bgates747/agon-extender/docs/tasks/README.md

# Project Tasks

This directory contains the tracked detail record for every item in `TODO.md`.
Task files hold scope, instructions, state, decisions, evidence, gotchas, and
validation requirements; `TODO.md` remains the authoritative task index.

Keep private network and filesystem topology, credentials, account data, and
unique device identifiers out of tracked tasks. Refer to an ignored local
record when such details are operationally necessary.

## Task silos and durable promotion

Use task directories as bounded work and review silos while scope, evidence,
and implementation shape are still emerging. Keeping each task's generators,
schemas, evidence, and provisional outputs together makes its contribution
discrete and auditable without prematurely declaring project-wide structure.

When a task-local result becomes recurring infrastructure or documentation,
promote it into a durable role-named location rather than leaving production
users dependent on a historical task number. Promotion preserves the task
record and accepted evidence, but the maintained interface, procedures, tools,
and canonical artifacts move under the subject they serve.

A durable construct may synthesize accepted work from several task silos. The
promotion task must identify the contributing authorities, remove competing
machine-readable sources of truth, update routine references, and preserve
traceability without copying task history into the production interface.

## Current documentation versus evidence

The [current handbook](../README.md) is the operating/design entry point for
humans and agents. When accepted work changes behavior, update its maintained
role-named guide in place so that it contains only currently accurate guidance.
Do not require readers to reconcile an old instruction with a later amendment.

Task records, dated experiments and historical decisions preserve provenance;
they are not competing current manuals. Move reusable guidance to its maintained
authority and link that authority from the task. Keep superseded instructions
in Git history or clearly separated evidence, not beneath a warning in the
current procedure. Unknown implementation/qualification limits remain explicit
current facts; do not erase those limits to make the handbook look finished.

## Actor-explicit proposals

The `TRS-80-NNN` namespace owns Extender integration work for TRS-80-derived
software and systems. `TRS-80-001` begins with TRS-OS on Agon; the namespace
does not imply that physical TRS-80 hardware or every TRS-80 model is supported.
`TODO.md` remains the sole authoritative unfinished-task index.

Every proposed contract, decision, task, procedure, and failure path must name
the actor performing each material action. Identify the applicable eZ80/MOS
component, onboard VDP/Pico-D4 firmware, EDP/P4 firmware, hardware circuit,
physical wiring, host tool, resident service, application, or operator rather
than assigning behavior vaguely to “the system” or “firmware.”

For communication, name the sender, receiver, transport owner, and physical
wiring where known. Distinguish the actor requesting an action from the actor
authorizing, executing, recording, observing, and recovering it. If ownership
is genuinely unresolved, say so explicitly and assign the decision to a
tracked task.

## Firmware defect identities

Use the stable `FWBUG-NNN` identity from [the firmware bug register](../firmware-bugs.md)
for a promoted defect task (`docs/tasks/FWBUG-NNN.md`), rather than renumbering
it. Register findings before implementation; link the originating task records
back to the register item and retain their historical finding IDs. Promotion
requires a corresponding TODO entry and bounded work contract; a bug register
entry alone does not start work.

## Tested acceptance closes into production

Explicit Author approval after testing authorizes the owning agent to promote
that accepted result into the maintained production location as part of closeout.
Package exact tested bytes, verify and retain the new immutable bundle, update
`production/current.yaml` and the current handbook/operating guides, then commit
and tag the promotion with the agreed production version. Keep rollback and
bounded evidence. Do not leave accepted deliverables only in a task silo.

The version must already be approved, or the agent must obtain that decision.
An annotated immutable Git tag identifies the commit containing the selected
bundle and documentation; push the commit and tag under the Author's repository
publication authorization. Existing tags and archived bundles are not rewritten.
See [versioning policy](../versions/README.md). This does not start unrelated
work or authorize public distribution of private/local-only archives.
