bgates747/agon-extender/docs/tasks/SETUP-006/SETUP-006.4-wiring-design/electrical-requirements.md

# SETUP-006.4 electrical requirements and candidate allocation

> **Historical task evidence:** HW-001 superseded this provisional allocation
> with the common-UART `light2-harness-r02` candidate. This file remains useful
> for predecessor evidence and requirement provenance but is not current wiring
> authority.

## Status and interpretation

- State: task-local review candidate
- Physical assembly: unchanged
- Author's completed Fritzing source draft: wiring and geometry preserved;
  embedded UART1 labels corrected by CA-2026-08-25-001
- Fritzing `draft_v1` derivative: generated for Author review
- Immediate target: Exclusive Extended beta transport
- Separate deferred target: Exclusive Compatible stock UART

This review turned the then-current firmware and mode requirements into
electrical design inputs. It does not approve a harness revision, claim that
the assembled bench matches the candidate, or authorize a physical test.

The generated `draft_v1` has separately been corrected and machine-audited as
a complete drawing of the controlled-power predecessor circuit under
AUDIT-002. It is evidence and a construction reference for that circuit, not a
claim that the fresh-design allocation below has already been drawn or
accepted.

The predecessor `light2-harness-r01` pin map and its runs are strong
evidence for the enhanced forward bus. They are not proof of assembled-system
safety and are not a stock-VDP UART design. The latter requires a later design
review after EMOS and EDP freeze its physical requirements.

## Pinned sources

1. Official VDP tag `v2.16.0`, commit
   `c7ac293d2aa81ddfa693390549bcd909069c8fc3`: `video/agon.h`,
   `video/vdp_protocol.h`, `video/vdu_sys.h`, and
   `video/vdu_stream_processor.h`.
2. Official MOS commit `5f67b1ca77eb7a77d3b37cc7b029db51f0d1548e`:
   `main.c`, `src/uart.c`, and `src/serial.asm`.
3. Olimex ESP32-P4-DevKit commit
   `4b453612bd72e2b83b49cb1156de93f655b8aec4`, Rev D1 schematic
   `HARDWARE/ESP32-P4-DevKit-Rev.D1/ESP32-P4-DevKit_Rev_D1.kicad_sch`.
4. Current project authorities: PORT-008, QUAL-002, the operating-mode audit,
   and `hardware/designs/light2-harness-r01/`.
5. TI's current SN74LV125A documentation identifies over-voltage-tolerant
   inputs and `Ioff` partial-power-down support. TI's SN74HC125 documentation
   identifies input clamp diodes and does not specify `Ioff`. At least four
   exact TI `SN74LV125AN` 14-PDIP parts are operator-confirmed on order. Receipt,
   physical count, and allocation to Extender remain unconfirmed because the
   separately ordered parts may be committed elsewhere.

## Contract layers

The phrase "compatible transport" must not collapse three different contracts:

1. **Application bytes:** EDP consumes the same VDU command bytes and emits the
   same VDP protocol packets as official VDP for retained functionality.
2. **EMOS behavior:** EMOS owns routing, response parsing, completion flags,
   sysvar updates, activation, committed mode, and recovery.
3. **Physical transport:** Exclusive Extended uses an eight-bit forward bus and
   a one-way UART return. It need not copy the onboard VDP's four-wire UART0
   circuit, but it must prove equivalent application-visible behavior, pacing,
   and recovery within the accepted mode contract.

Official VDP uses 1,152,000-baud 8-N-1 UART, begins with RTS flow control, and
can enable CTS/RTS full duplex. Official MOS UART0 provides RX, TX, RTS, and CTS
on Port D bits 0 through 3. Current official MOS UART1 provides PC0 TX and PC1
RX, while its hardware-flow helper configures PC3 only as CTS input; it does
not currently provide a UART1 RTS output on PC2. Exclusive Extended therefore
cannot assume that stock UART0 electrical flow control exists on UART1.

## Immediate beta signal inventory

### Mandatory conductors and local controls
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
