bgates747/agon-extender/docs/tasks/QUAL-003/debrief/P01h/codec-screen/discussion/2026-09-17-gemini-architecture.md

### Architectural Specification: Agon Light/Console 8 ESP32-P4 Extender Board

This document defines the system architecture, dual-core resource allocation, memory maps, and configuration parameters for using the **Olimex ESP32-P4-DevKit-Rev-D1** as a high-performance Video Display Processor (VDP) network extender for the **Agon Light 2** and **Heber Console 8** (eZ80F92/F91). 

### 1. System Architecture & Dual-Core Topology

To sustain a **512x384 1bpp single-buffered framebuffer** transmission over a 100 Mbps RMII Ethernet link without blocking or lagging real-time command processing from the eZ80, the system relies on strict **Symmetric Multiprocessing (SMP)** segregation. 

                  +---------------------------------------+

                  |         eZ80 Host Computer            |
                  +---------------------------------------+
                                      |
                                      | (UART over Port C Pins)
                                      v
+-------------------------------------------------------------------------+

| Olimex ESP32-P4 Extender Board                                          |
|                                                                         |
|  +-----------------------------------+   +----------------------------+ |
|  | Core 1 (APP_CPU): VDP Emulation   |   | Core 0 (PRO_CPU): Network  | |
|  |-----------------------------------|   |----------------------------| |
|  | * Deep Internal SRAM UART FIFO    |   | * LwIP TCP/IP Stack        | |
|  | * Decodes Agon VDP Packets        |   | * Ethernet MAC/PHY Drivers | |
|  | * Modifies Live Framebuffer       |   | * Lockless Frame Snapshot  | |
|  +-----------------------------------+   +----------------------------+ |
|                    |                                    ^               |
|                    v (Direct Write)                     | (Lockless Copy|
|        +-----------------------+                        |  sub-uS speed)|
|        | vdp_framebuffer       |------------------------+               |
|        | (24 KB Aligned SRAM)  |                                        |
|        +-----------------------+                                        |
|                                                                         |
|  +--------------------------------------------------------------------+ |
|  | GDMA & Network Hardware Layer                                      | |
|  |--------------------------------------------------------------------| |
|  | Outbound Stream Buffer (Internal SRAM)                             | |
|  | LAN8720 RMII Ethernet Controller Interface                         | |
|  +--------------------------------------------------------------------+ |
+-------------------------------------------------------------------------+
                                      |
                                      v
                         +--------------------------+

                         | Network Target / Client  |
                         +--------------------------+
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
