bgates747/agon-extender/docs/tasks/BENCH-001/evidence/driving-hour.png

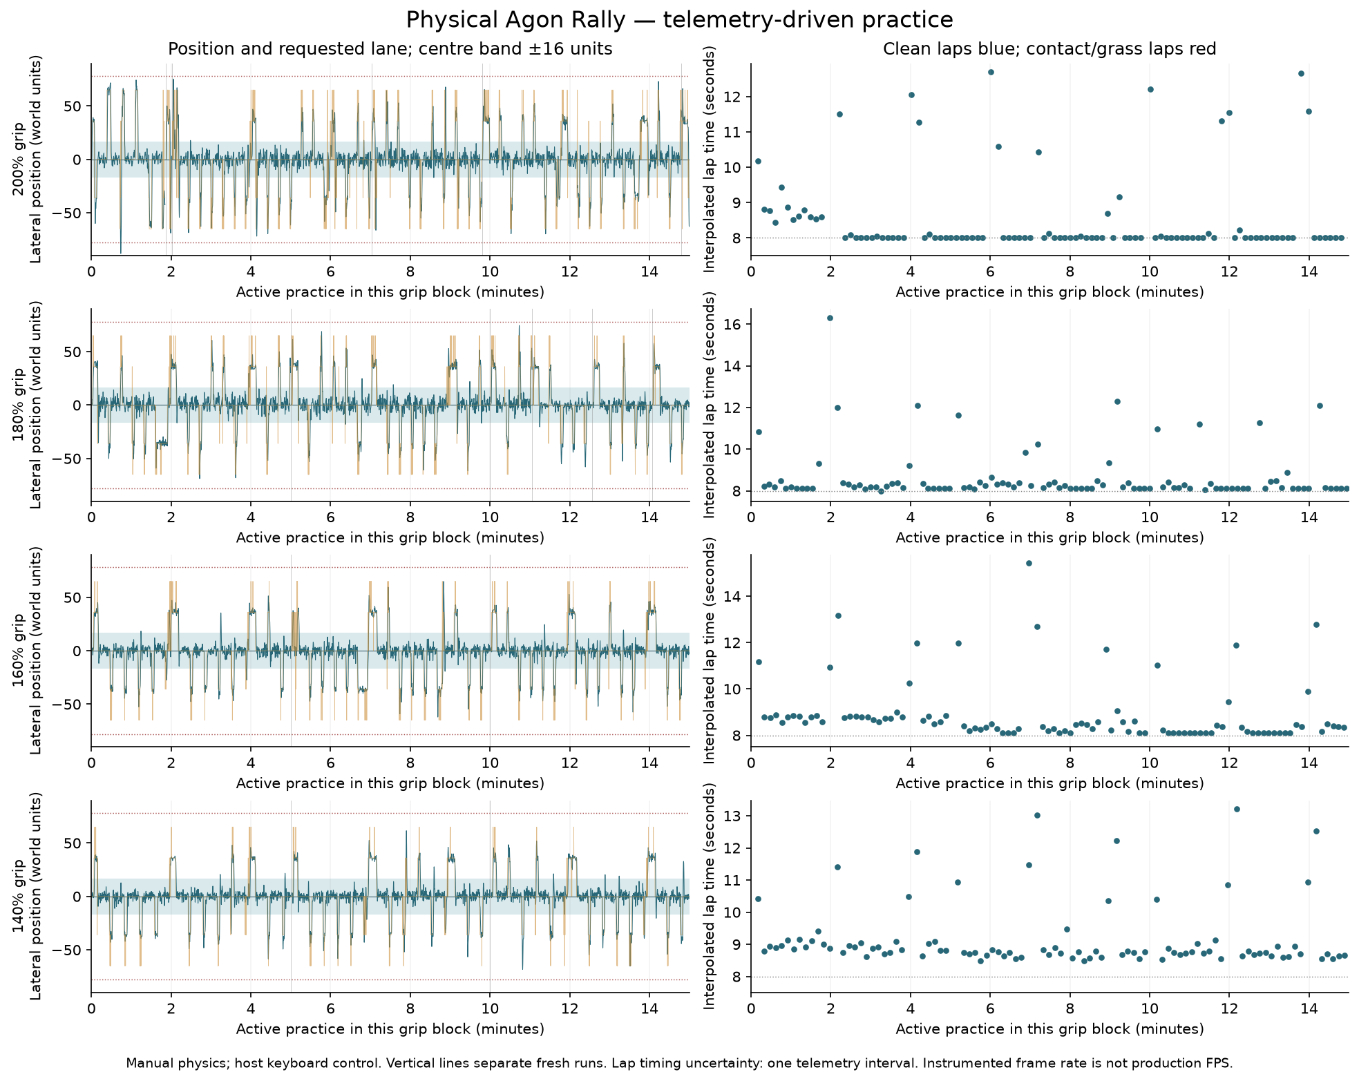
docs/tasks/BENCH-001/evidence/driving-hour.png
