bgates747/agon-extender/docs/tasks/QUAL-003/debrief/P01f/A/rtos-tasks.png

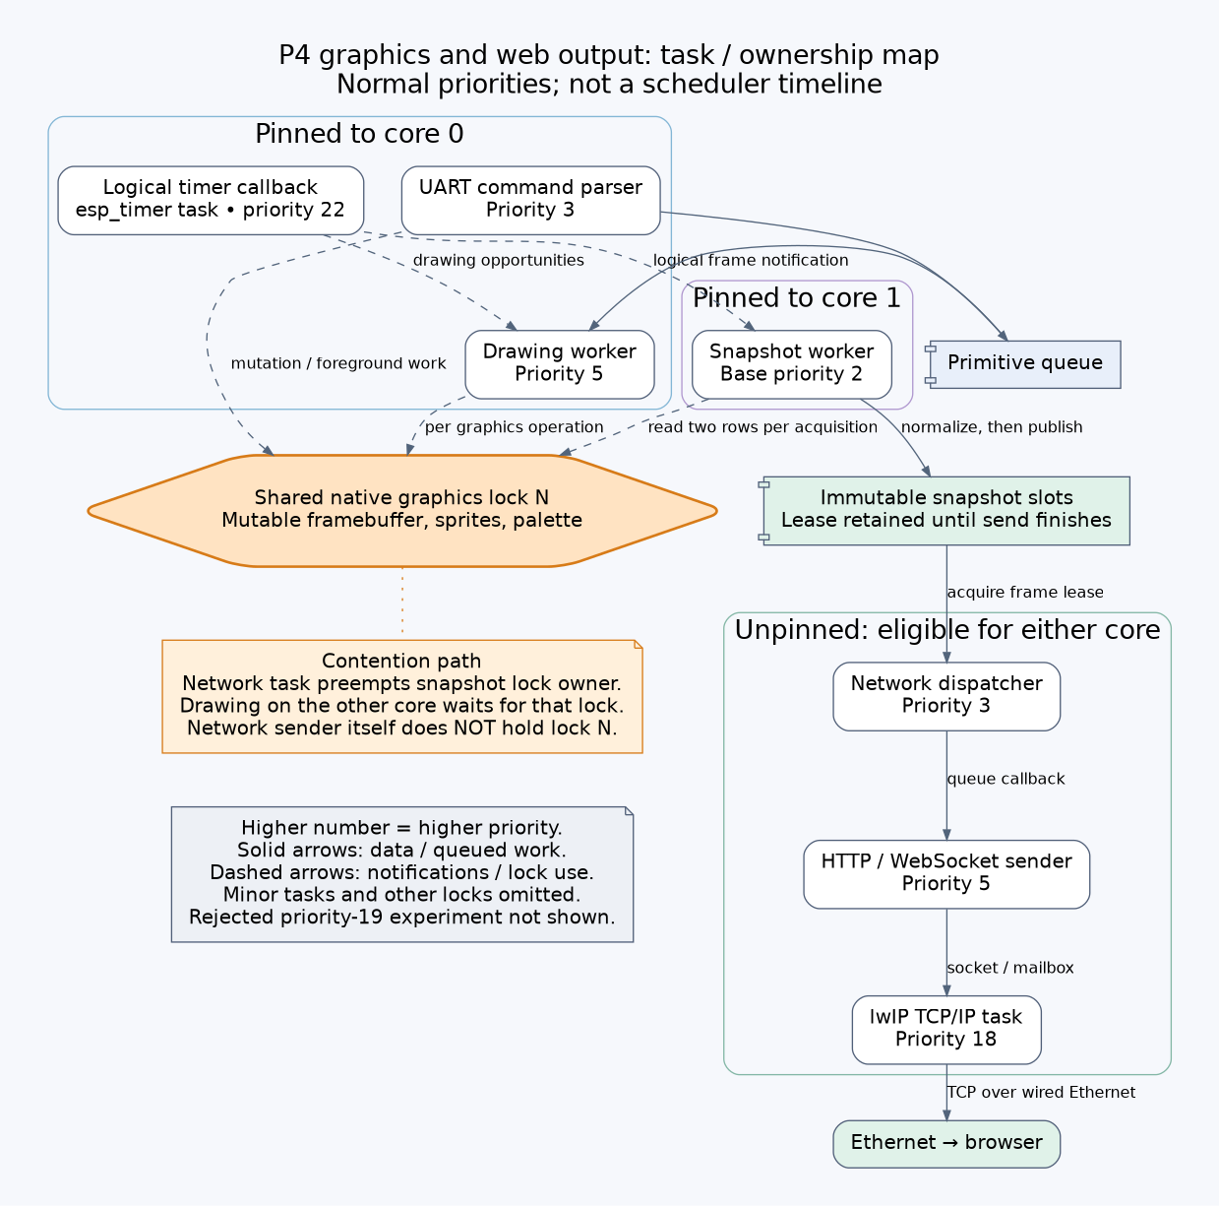
docs/tasks/QUAL-003/debrief/P01f/A/rtos-tasks.png
