bgates747/agon-extender/docs/tasks/QUAL-003/debrief/P01g/ladder.png

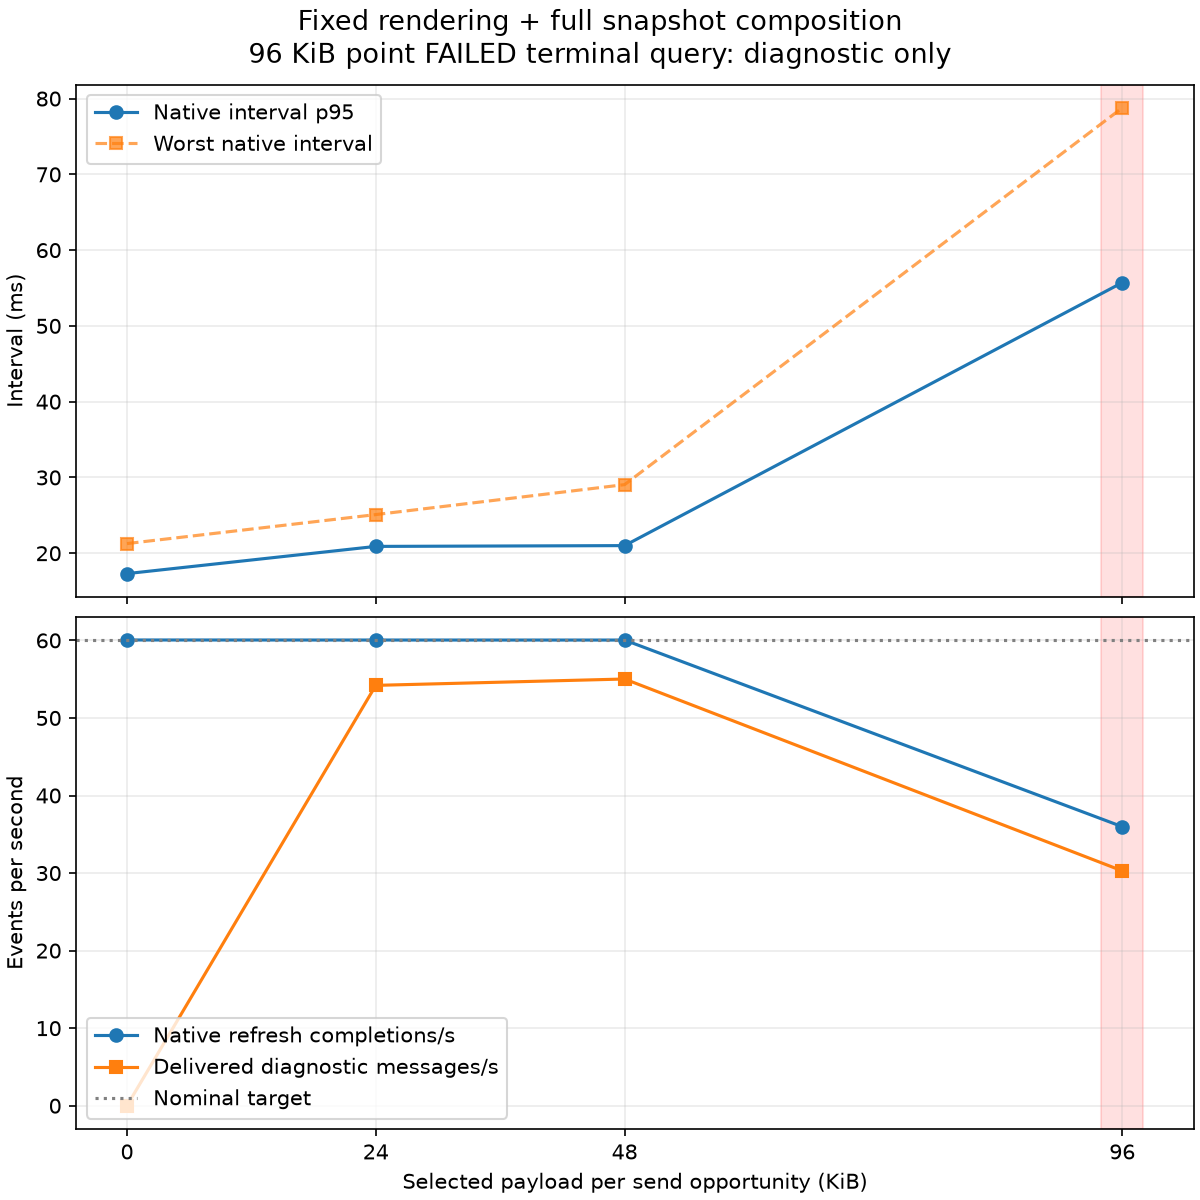
docs/tasks/QUAL-003/debrief/P01g/ladder.png
