bgates747/agon-extender/docs/tasks/QUAL-003/debrief/P01h/codec-screen/image-p4/images/nurples-jpeg90.png

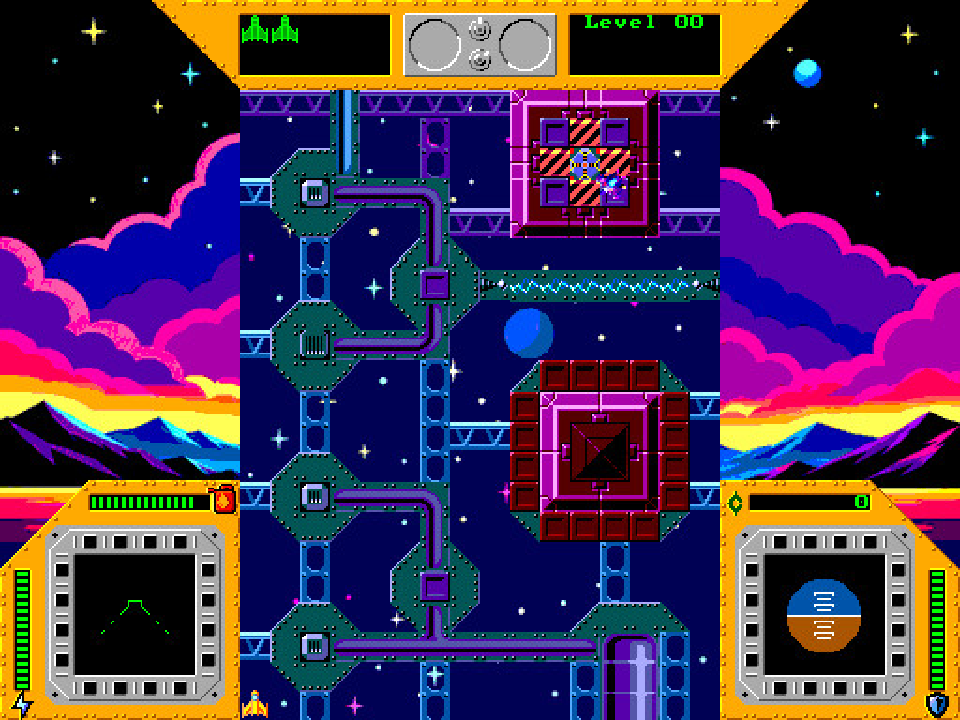
docs/tasks/QUAL-003/debrief/P01h/codec-screen/image-p4/images/nurples-jpeg90.png
