bgates747/agon-extender/docs/tasks/QUAL-003/debrief/P01h/evidence/raw_sprites-r06.png

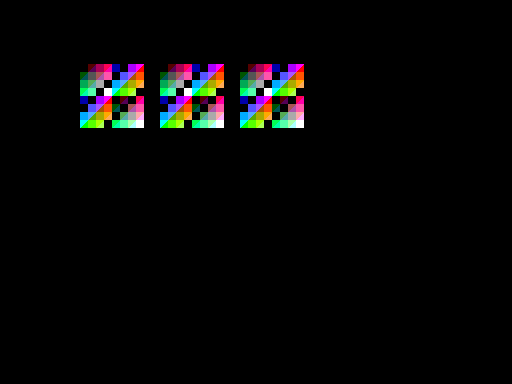
docs/tasks/QUAL-003/debrief/P01h/evidence/raw_sprites-r06.png
