bgates747/agon-extender/docs/tasks/QUAL-003/debrief/P01h/srle2/web/evidence/final/rejected-frame-retains-image.png

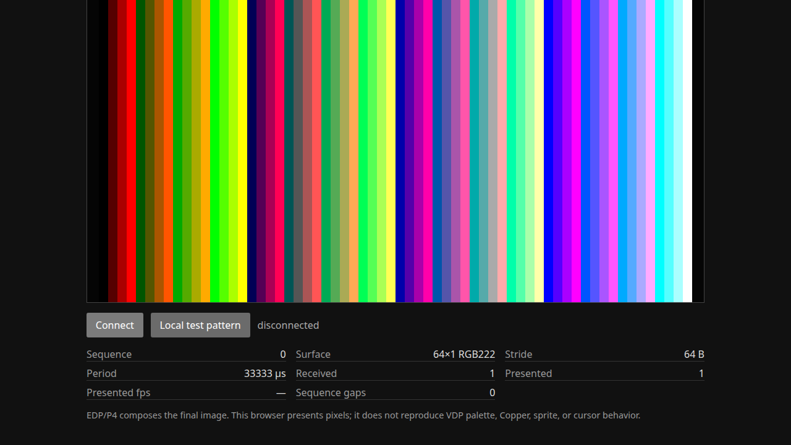
docs/tasks/QUAL-003/debrief/P01h/srle2/web/evidence/final/rejected-frame-retains-image.png
