bgates747/agon-extender/docs/tasks/QUAL-004/evidence/bounded-corpus/BSP26_01-a2/BSP26_01/mainboard.png

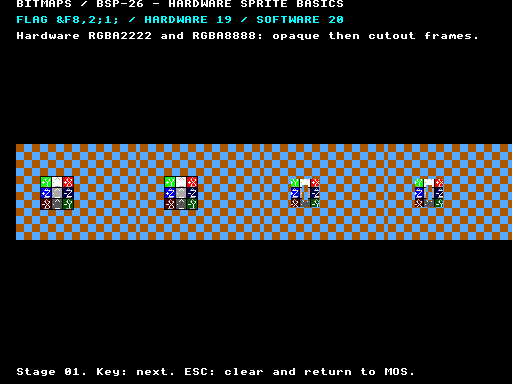
docs/tasks/QUAL-004/evidence/bounded-corpus/BSP26_01-a2/BSP26_01/mainboard.png
