bgates747/agon-extender/docs/tasks/QUAL-004/evidence/bounded-corpus/BSP26_02-a1/BSP26_02/mainboard.png

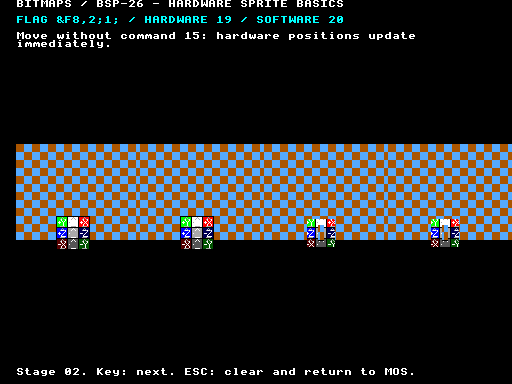
docs/tasks/QUAL-004/evidence/bounded-corpus/BSP26_02-a1/BSP26_02/mainboard.png
