bgates747/agon-extender/docs/tasks/QUAL-004/evidence/bounded-corpus/BSP26_03-a1/BSP26_03/mainboard.png

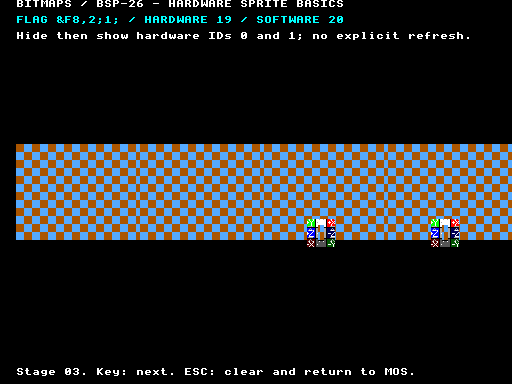
docs/tasks/QUAL-004/evidence/bounded-corpus/BSP26_03-a1/BSP26_03/mainboard.png
