bgates747/agon-extender/docs/tasks/QUAL-004/evidence/bounded-corpus/BSP27_01-a1/BSP27_01/mainboard.png

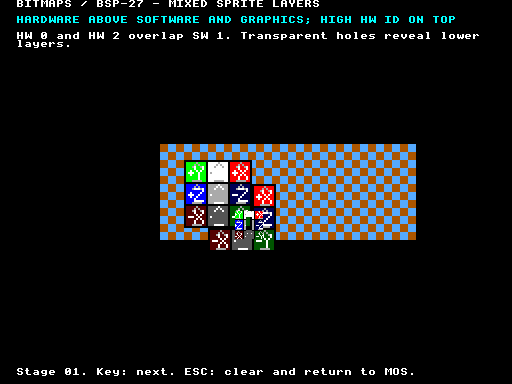
docs/tasks/QUAL-004/evidence/bounded-corpus/BSP27_01-a1/BSP27_01/mainboard.png
