bgates747/agon-extender/docs/tasks/QUAL-004/evidence/bounded-corpus/CLIPROW-a1/CLIPROW/mainboard.png

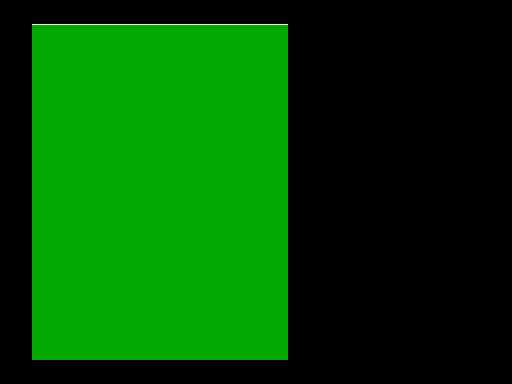
docs/tasks/QUAL-004/evidence/bounded-corpus/CLIPROW-a1/CLIPROW/mainboard.png
