bgates747/agon-extender/docs/tasks/QUAL-004/evidence/bounded-corpus/SHP01-a1/SHP01/mainboard.png

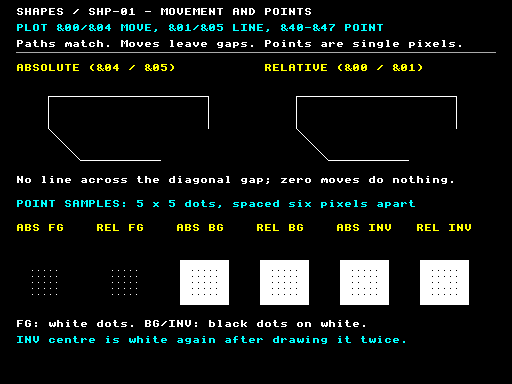
docs/tasks/QUAL-004/evidence/bounded-corpus/SHP01-a1/SHP01/mainboard.png
