bgates747/agon-extender/docs/tasks/QUAL-004/evidence/bounded-corpus/SHP02-a1/SHP02/mainboard.png

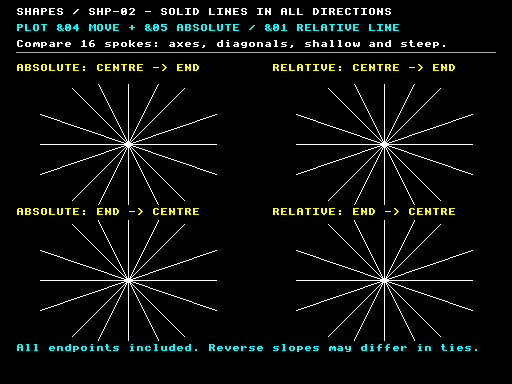
docs/tasks/QUAL-004/evidence/bounded-corpus/SHP02-a1/SHP02/mainboard.png
