bgates747/agon-extender/docs/tasks/QUAL-004/evidence/bounded-corpus/SHP03-a1/SHP03/mainboard.png

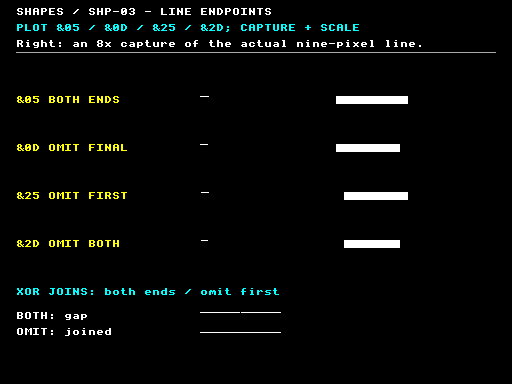
docs/tasks/QUAL-004/evidence/bounded-corpus/SHP03-a1/SHP03/mainboard.png
