bgates747/agon-extender/docs/tasks/QUAL-004/evidence/bounded-corpus/SHP04-a1/SHP04/mainboard.png

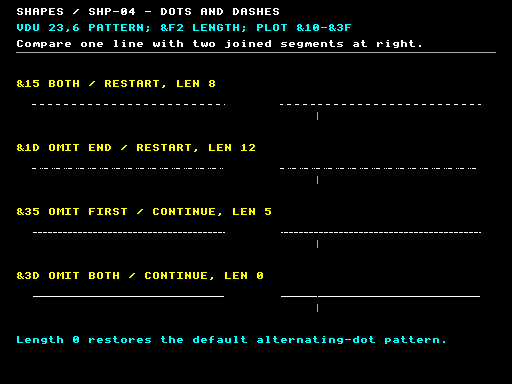
docs/tasks/QUAL-004/evidence/bounded-corpus/SHP04-a1/SHP04/mainboard.png
