bgates747/agon-extender/docs/tasks/QUAL-004/evidence/bounded-corpus/SHP05-a1/SHP05/mainboard.png

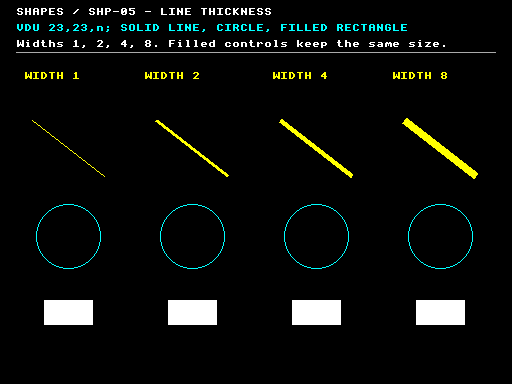
docs/tasks/QUAL-004/evidence/bounded-corpus/SHP05-a1/SHP05/mainboard.png
