bgates747/agon-extender/docs/tasks/QUAL-004/evidence/bounded-corpus/SHP06-a1/SHP06/mainboard.png

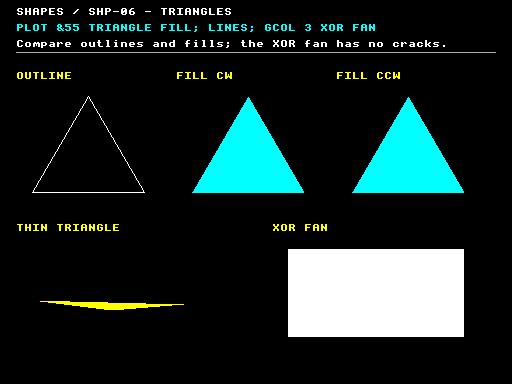
docs/tasks/QUAL-004/evidence/bounded-corpus/SHP06-a1/SHP06/mainboard.png
