bgates747/agon-extender/docs/tasks/QUAL-004/evidence/bounded-corpus/SHP07-a1/SHP07/mainboard.png

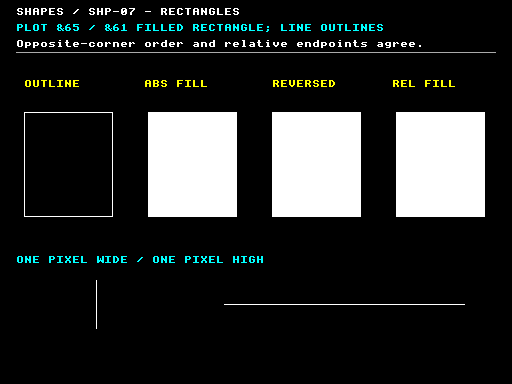
docs/tasks/QUAL-004/evidence/bounded-corpus/SHP07-a1/SHP07/mainboard.png
