bgates747/agon-extender/docs/tasks/QUAL-004/evidence/bounded-corpus/SHP08-a1/SHP08/mainboard.png

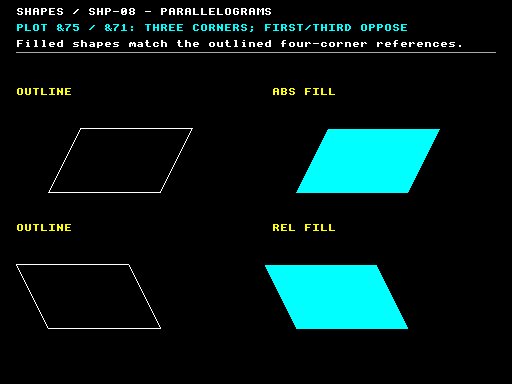
docs/tasks/QUAL-004/evidence/bounded-corpus/SHP08-a1/SHP08/mainboard.png
