bgates747/agon-extender/docs/tasks/QUAL-004/evidence/bounded-corpus/SHP09-a1/SHP09/mainboard.png

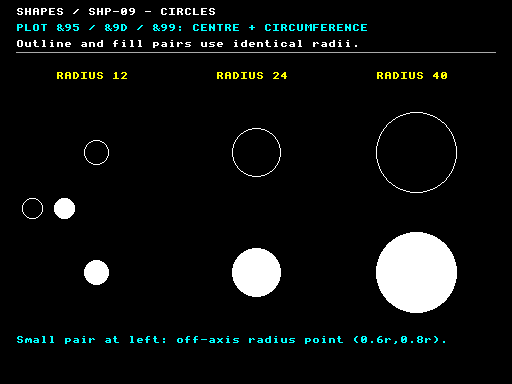
docs/tasks/QUAL-004/evidence/bounded-corpus/SHP09-a1/SHP09/mainboard.png
