bgates747/agon-extender/docs/tasks/QUAL-004/evidence/bounded-corpus/SHP10-a1/SHP10/mainboard.png

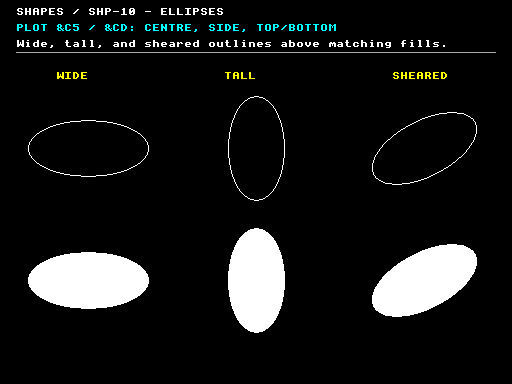
docs/tasks/QUAL-004/evidence/bounded-corpus/SHP10-a1/SHP10/mainboard.png
