bgates747/agon-extender/docs/tasks/QUAL-004/evidence/bounded-corpus/SHP11-a1/SHP11/mainboard.png

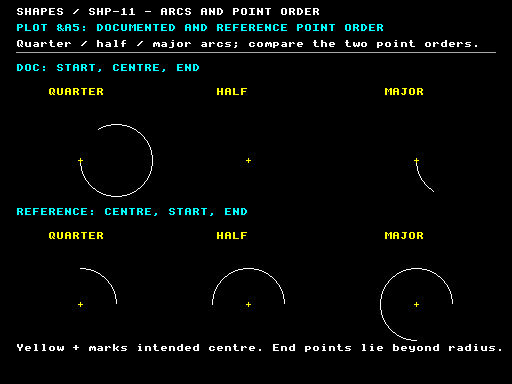
docs/tasks/QUAL-004/evidence/bounded-corpus/SHP11-a1/SHP11/mainboard.png
