bgates747/agon-extender/docs/tasks/QUAL-004/evidence/bounded-corpus/SHP12-a1/SHP12/mainboard.png

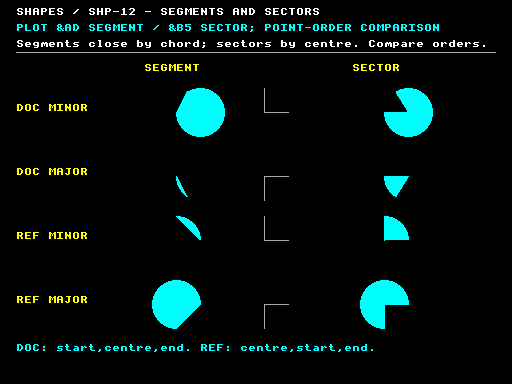
docs/tasks/QUAL-004/evidence/bounded-corpus/SHP12-a1/SHP12/mainboard.png
