bgates747/agon-extender/docs/tasks/QUAL-004/evidence/bounded-corpus/SHP13-a1/SHP13/mainboard.png

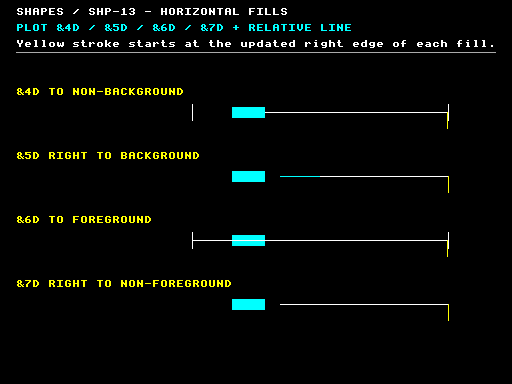
docs/tasks/QUAL-004/evidence/bounded-corpus/SHP13-a1/SHP13/mainboard.png
