bgates747/agon-extender/docs/tasks/QUAL-004/evidence/bounded-corpus/SHP14-a1/SHP14/mainboard.png

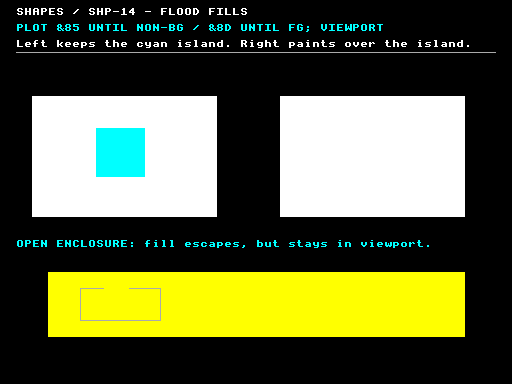
docs/tasks/QUAL-004/evidence/bounded-corpus/SHP14-a1/SHP14/mainboard.png
