bgates747/agon-extender/docs/tasks/QUAL-004/evidence/bounded-corpus/SHP15-a1/SHP15/mainboard.png

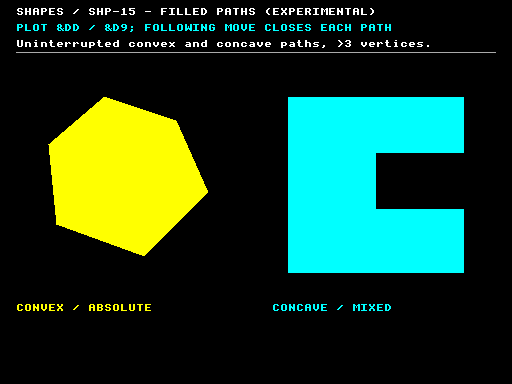
docs/tasks/QUAL-004/evidence/bounded-corpus/SHP15-a1/SHP15/mainboard.png
