bgates747/agon-extender/docs/tasks/QUAL-004/evidence/bounded-corpus/SHP16-a1/SHP16/mainboard.png

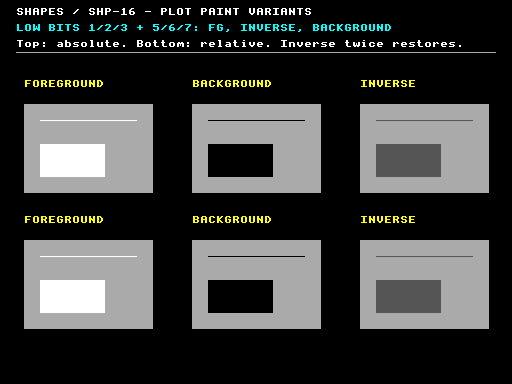
docs/tasks/QUAL-004/evidence/bounded-corpus/SHP16-a1/SHP16/mainboard.png
