bgates747/agon-extender/docs/tasks/QUAL-004/evidence/bounded-corpus/SHP17-a1/SHP17/mainboard.png

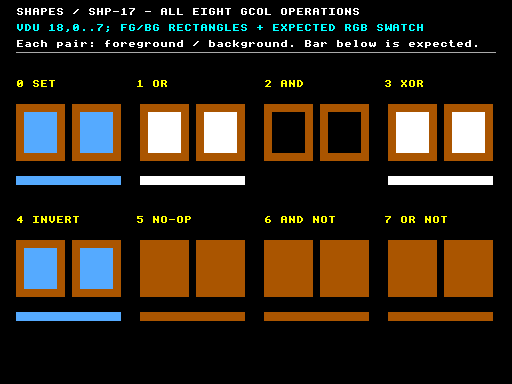
docs/tasks/QUAL-004/evidence/bounded-corpus/SHP17-a1/SHP17/mainboard.png
