bgates747/agon-extender/docs/tasks/QUAL-004/evidence/bounded-corpus/SHP18-a1/SHP18/mainboard.png

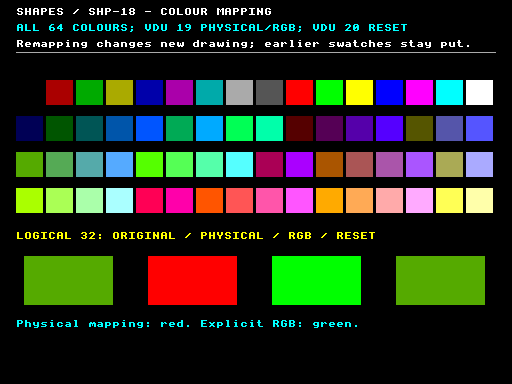
docs/tasks/QUAL-004/evidence/bounded-corpus/SHP18-a1/SHP18/mainboard.png
