bgates747/agon-extender/docs/tasks/QUAL-004/evidence/bounded-corpus/SHP19-a1/SHP19/mainboard.png

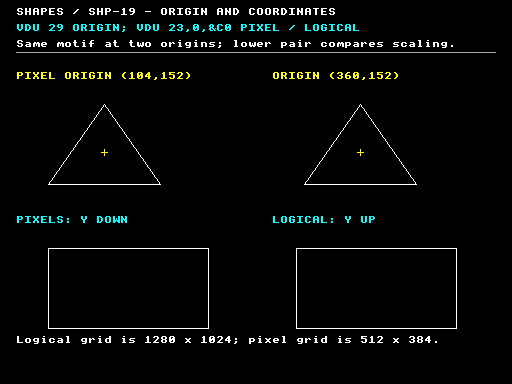
docs/tasks/QUAL-004/evidence/bounded-corpus/SHP19-a1/SHP19/mainboard.png
