bgates747/agon-extender/docs/tasks/QUAL-004/evidence/bounded-corpus/SHP21-a1/SHP21/mainboard.png

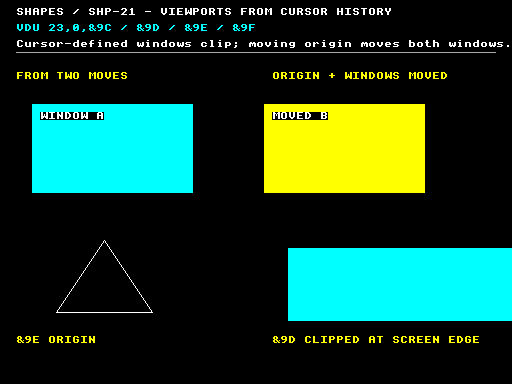
docs/tasks/QUAL-004/evidence/bounded-corpus/SHP21-a1/SHP21/mainboard.png
