bgates747/agon-extender/docs/tasks/QUAL-004/evidence/bounded-corpus/SHP22-a1/SHP22/mainboard.png

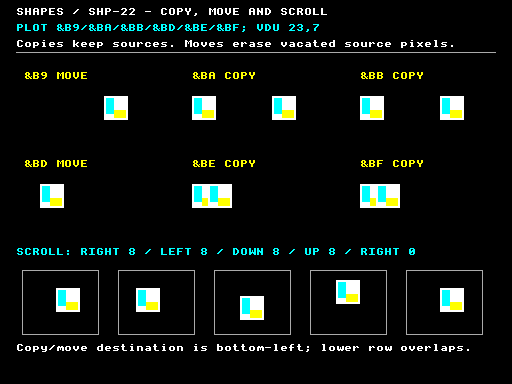
docs/tasks/QUAL-004/evidence/bounded-corpus/SHP22-a1/SHP22/mainboard.png
