bgates747/agon-extender/docs/tasks/QUAL-004/evidence/bounded-corpus/SHP24-a1/SHP24/mainboard.png

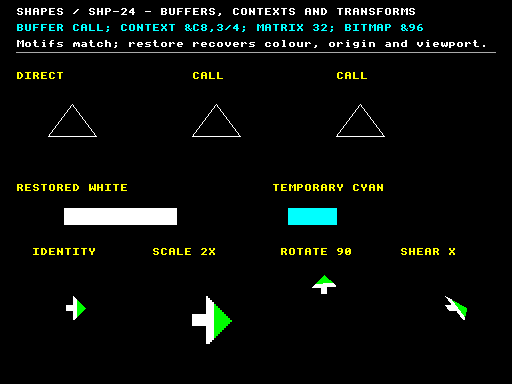
docs/tasks/QUAL-004/evidence/bounded-corpus/SHP24-a1/SHP24/mainboard.png
