bgates747/agon-extender/docs/tasks/QUAL-004/evidence/mode-controls/mode9-run02/COP16_EDIT/mainboard.png

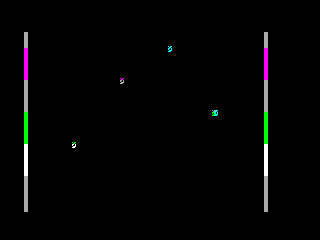
docs/tasks/QUAL-004/evidence/mode-controls/mode9-run02/COP16_EDIT/mainboard.png
