bgates747/agon-extender/docs/tasks/QUAL-004/evidence/unfenced-alpha/mainboard-repeat-0.png

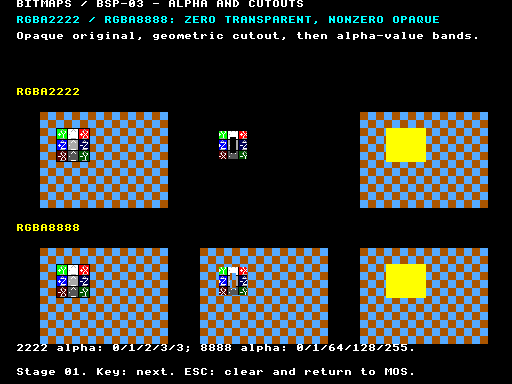
docs/tasks/QUAL-004/evidence/unfenced-alpha/mainboard-repeat-0.png
