bgates747/agon-extender/docs/tasks/QUAL-004/evidence/unfenced-alpha/repeat-difference.png

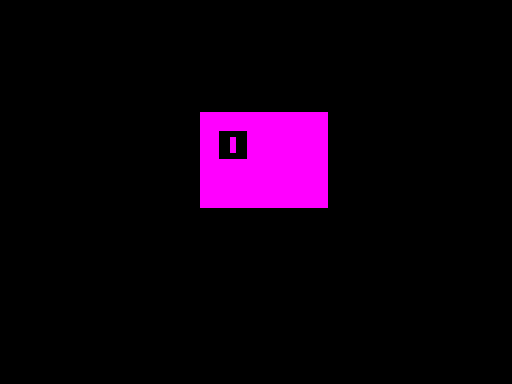
docs/tasks/QUAL-004/evidence/unfenced-alpha/repeat-difference.png
