bgates747/agon-extender/docs/tasks/QUAL-004/packed-expansion/evidence/capture/PACK10.png

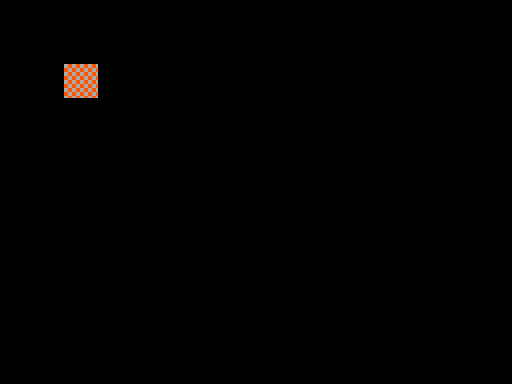
docs/tasks/QUAL-004/packed-expansion/evidence/capture/PACK10.png
