bgates747/agon-extender/docs/tasks/QUAL-004/page-controls/evidence/PAGE_SWAP/mainboard.png

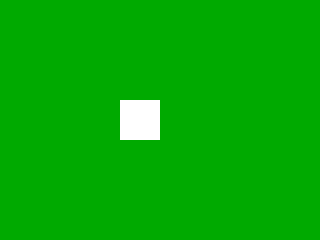
docs/tasks/QUAL-004/page-controls/evidence/PAGE_SWAP/mainboard.png
