bgates747/agon-extender/docs/tasks/QUAL-004/sprite-scroll/extender-followup/evidence/SS_EDGES/comparison/mainboard.png

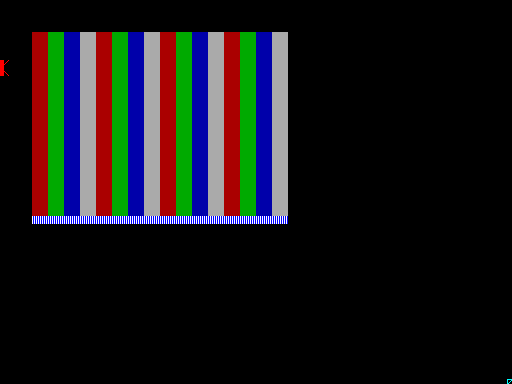
docs/tasks/QUAL-004/sprite-scroll/extender-followup/evidence/SS_EDGES/comparison/mainboard.png
