bgates747/agon-extender/docs/tasks/QUAL-004/teletext/evidence/TTSTATIC/mainboard.png

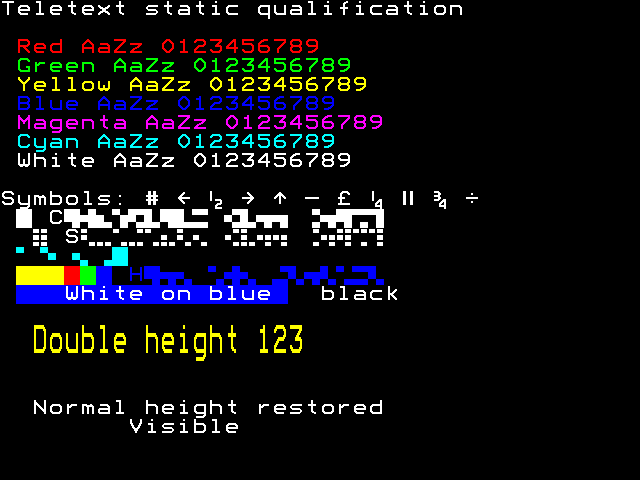
docs/tasks/QUAL-004/teletext/evidence/TTSTATIC/mainboard.png
