bgates747/agon-extender/social-preview-upload.png

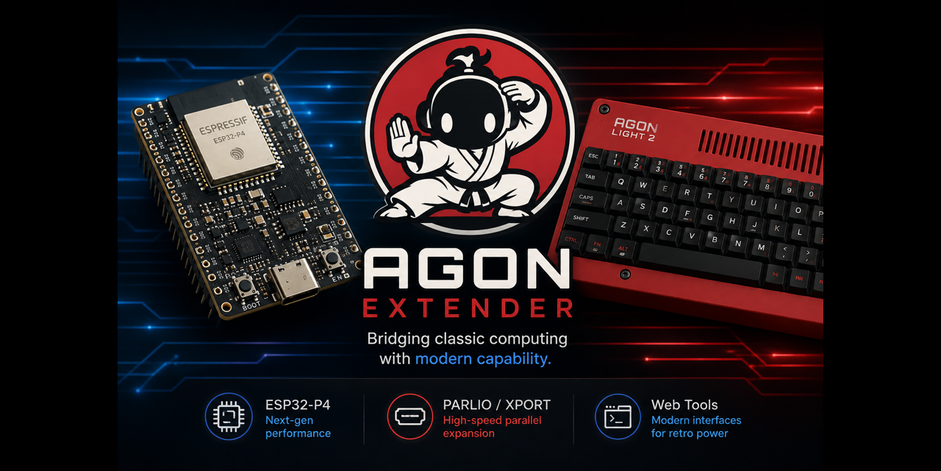
social-preview-upload.png
