bgates747/agon-extender/social-preview.png

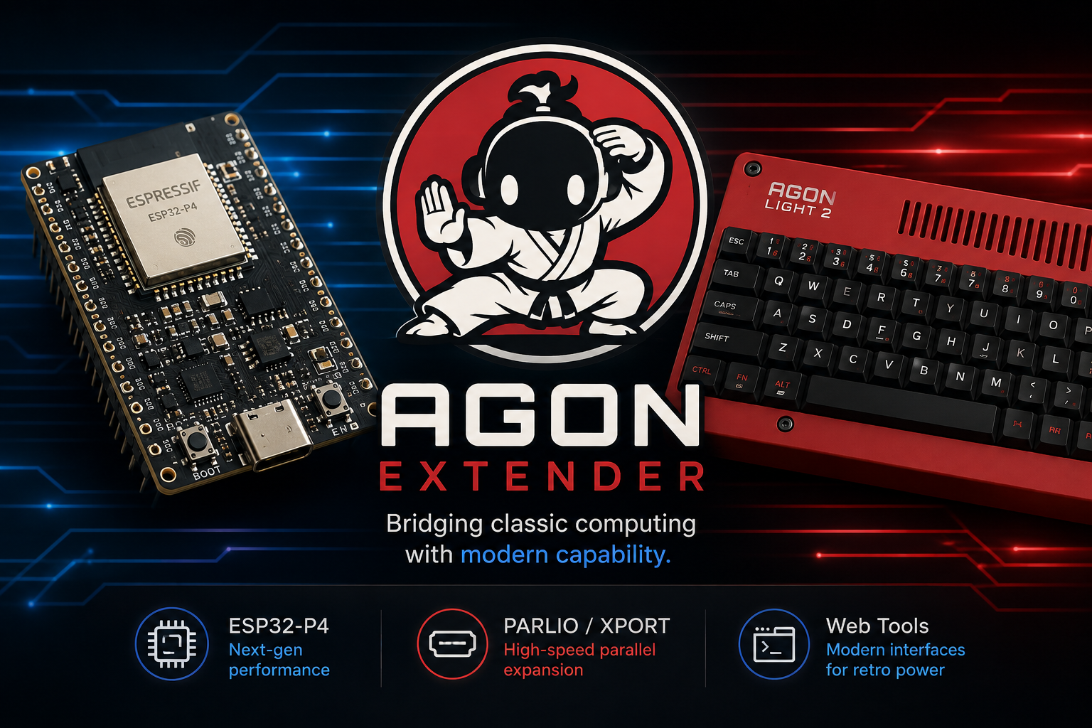
social-preview.png
