bgates747/agon-extender/hardware/designs/light2-harness-r02/BOM.md

<!-- Generated by generate_bom.py from bom.yaml; do not edit. -->
# Light 2 harness r02 bill of materials

This BOM describes one `light2-harness-r02` circuit build. Its lifecycle status is **candidate**. Electrical connectivity and nominal values remain authoritative in `connectivity.yaml`; this document is a checked procurement projection.

The Author froze this BOM under `HW-001-D009` at `2026-08-29T23:05:52+00:00`.

## Fitted circuit components

| Line ID | Qty | References | Part or value | Package / procurement constraint | Role |
|---|---:|---|---|---|---|
| `ic-sn74lvc244an` | 2 | `U1, U2` | `SN74LVC244AN` | PDIP-20; Exact part number; N suffix is the through-hole PDIP package. | Agon-powered forward UART, parallel-data, CLOCK, and VALID_N buffering. |
| `ic-sn74lv125an` | 2 | `U3, U4` | `SN74LV125AN` | PDIP-14; Exact part number; N suffix is the through-hole PDIP package. | Agon-powered UART return and P4-powered low-only isolated controls. |
| `resistor-220r-1pct` | 13 | `R1, R2, R3, R4, R5, R6, R7, R8, R9, R10, R11, R12, R13` | `220 ohm` | axial through-hole; 220 ohm, 1% tolerance or better; breadboard-compatible lead size. | Replaceable source-series protection and damping on every driven transport output. |
| `resistor-47k-1pct` | 8 | `R14, R15, R16, R17, R18, R19, R20, R21` | `47 kohm` | axial through-hole; 47 kilohm, 1% tolerance or better; breadboard-compatible lead size. | P4 data and shared-UART inactive-state bias. |
| `resistor-10k-1pct` | 10 | `R22, R23, R24, R25, R26, R27, R28, R29, R30, R31` | `10 kohm` | axial through-hole; 10 kilohm, 1% tolerance or better; breadboard-compatible lead size. | CLOCK, VALID_N, READY_N, output-enable, and P4 control default-state bias. |
| `capacitor-100nf-ceramic` | 4 | `C1, C2, C3, C4` | `100 nF` | radial through-hole; Nonpolar ceramic, at least 6.3 V rating, breadboard-compatible lead spacing. | One local supply bypass capacitor at each logic IC. |
| `capacitor-1uf-ceramic` | 2 | `C5, C6` | `1 uF` | radial through-hole; Nonpolar ceramic, at least 6.3 V rating, breadboard-compatible lead spacing. | One local bulk capacitor for each independent 3.3 V power domain. |

**Fitted total:** 41 discrete components across 7 procurement lines.

## Supplied equipment and modeled interfaces

| Qty | Equipment | Model references | Disposition |
|---:|---|---|---|
| 1 | Agon Light 2 | `J1` | External host equipment; not consumed by the Extender circuit build. |
| 1 | Olimex ESP32-P4-DevKit Rev D1 | `J2, J3` | Extender processor board; its EXT1 and EXT2 interfaces are represented by J2 and J3. |

## Exclusions

1. solderless breadboards and power rails.
2. IC sockets.
3. ribbon cable, hookup wire, and jumpers.
4. physical headers, receptacles, and strain relief.
5. test points, probe clips, and qualification instrumentation.
6. production PCB, enclosure, and mounting hardware.

These physical-assembly items remain outside this design BOM until the r02 breadboard construction authority fixes their exact form and quantity.

## Machine-readable sources

1. `bom.yaml` is the maintained procurement input.
2. `bom.csv` is a flat generated import view suitable for inventory or ERP mapping.
3. `connectivity.yaml` is the frozen electrical authority.
