bgates747/agon-extender/docs/tasks/SETUP-004/disposition-matrix.md

<!-- Generated by scripts/generate-subsystem-inventory.py; do not hand-edit. -->
# SETUP-004 disposition matrix

Review status is tracked per candidate. Detailed mechanical facts, reviewed
conclusions, and agent entry points are in
`generated/subsystem-inventory.yaml`.

Input digest: `8d8520de563a889538737dc50a5ba0e82d0e2bdc7560bbb0c98fb98eff73063a`

| Work | Candidate | Layer | Physical owner | Disposition | Review | Rationale |
|---|---|---|---|---|---|---|
| SETUP-004.1.a | Arduino core types and utility compatibility | Arduino core API | Extender P4 firmware runtime | RETAIN | ACCEPTED | These are source-level compatibility contracts shared by vendored code. |
| SETUP-004.1.a | Arduino sketch lifecycle and top-level startup | Arduino runtime | Extender P4 firmware runtime | RETAIN | ACCEPTED | The accepted hybrid framework deliberately preserves Arduino lifecycle idioms and the physical canary qualified Arduino autostart on the P4. |
| SETUP-004.1.a | Arduino Stream and Print-compatible byte-stream contract | Arduino core API | Extender P4 firmware runtime | RETAIN | ACCEPTED | Stream is the principal existing seam between VDP semantics and physical transport. |
| SETUP-004.1.a | Arduino monotonic timing and delay services | Arduino core API | Extender P4 firmware runtime | RETAIN | ACCEPTED | The pinned Arduino core supplies these portable APIs on P4. |
| SETUP-004.1.a | DBGSerial maintenance and operator binding | Arduino device API | Onboard VDP in legacy and applicable cooperative operation; none on Extender v1 | OMIT | ACCEPTED | Extender v1 omits the stock local maintenance/operator serial facility. |
| SETUP-004.1.a | FreeRTOS tasks, queues, semaphores, timers, and notifications | FreeRTOS through ESP-IDF | Extender P4 firmware runtime | RETAIN | ACCEPTED | ESP-IDF 5.5.5 supplies FreeRTOS on P4 and the accepted hybrid canary requires its 1000 Hz tick. |
| SETUP-004.1.a | ESP-IDF interrupt, ISR, and critical-section services | ESP-IDF hardware abstraction | Extender P4 hardware drivers | RETAIN | ACCEPTED | ESP-IDF 5.5.5 provides these services on P4, so retain the portable abstraction and ISR/task handoff patterns. |
| SETUP-004.1.a | ESP-IDF OTA partition and restart primitives | ESP-IDF system API | Extender P4 firmware and bootloader | RETAIN | ACCEPTED | The accepted Extender flash layout reserves two OTA slots and ADR-0007 requires ESP-IDF image validity and rollback integration. |
| SETUP-004.1.a | Primary VDP protocol serial binding | Arduino device API | Extender forward command transport and UART return transport | REPLACE | ACCEPTED | Rev 1 uses a high-speed forward path for command input and UART for return traffic, so the stock single-duplex Serial2 binding cannot remain. |
| SETUP-004.1.a | Arduino PSRAM and ESP-IDF capability-heap services | Arduino-ESP32 and ESP-IDF memory API | Extender P4 memory subsystem | RETAIN | ACCEPTED | The P4 profile has qualified 32 MiB PSRAM and the pinned hybrid framework supplies both API families. |
| SETUP-004.1.a | Stock VDP serial updater command path | VDP command service | No Extender v1 implementation; onboard VDP only in legacy or applicable cooperative operation | OMIT | ACCEPTED | The Author has already excluded the stock updater and DBGSerial-owned maintenance facilities from Extender v1. |
| SETUP-004.1.a | Unused Arduino WiFi include | Arduino library API | none | OMIT | ACCEPTED | The validated source scan finds WiFi.h only at this include and no WiFi API consumer. |
| SETUP-004.1.a | ESP32 watchdog and core-control policy | Arduino-ESP32 and ESP-IDF platform API | Extender P4 firmware runtime | REPLACE | ACCEPTED | Preserve the intent—long-running VDP tasks remain schedulable and supervised—but replace inherited global watchdog disabling and ESP32-era core assumptions with one explicit P4 task/watchdog policy. |
| SETUP-004.1.b | Unused vdp-gl DS3231 I2C RTC driver | vdp-gl device driver | No DS3231 device exists in the selected Extender v1 or stock Agon hardware baseline | OMIT | ACCEPTED | The official RTC service uses ESP32Time, not this hardware driver. |
| SETUP-004.1.b | Unused vdp-gl MCP23S17 SPI GPIO-expander driver | vdp-gl device driver | No MCP23S17 device exists in the selected Extender v1 or stock Agon hardware baseline | OMIT | ACCEPTED | The driver serves no selected Extender v1 hardware or stock-compatible behavior. |
| SETUP-004.1.b | ESP32Time software-clock provider | Arduino/POSIX time service | Extender P4 system clock when the EDP owns RTC behavior | RETAIN | ACCEPTED | Retaining this thin, already-vendored provider minimizes divergence from upstream and uses normal P4 system-time facilities. |
| SETUP-004.1.b | Stock VDP RTC command, packet, variables, and callbacks | VDP protocol and state | MOS owns canonical sysvar storage; the onboard VDP or EDP may supply RTC response data only through the selected mode-specific route | RETAIN | ACCEPTED | The stock RTC command, six-byte payload, wire framing, variable, and callback semantics are normal application-visible VDP behavior and belong inside the EDP-exclusive backward-compatibility contract. |
| SETUP-004.1.c | ESP32 CPU/APB clock and cycle-counter utilities | Architecture-specific timing utility | Extender P4 timing and clock hardware | REPLACE | ACCEPTED | Preserve required timing semantics at existing call seams while replacing ESP32/Xtensa register and frequency assumptions with P4-native implementations. |
| SETUP-004.1.c | vdp-gl pinned-core interrupt allocation helper | ESP-IDF interrupt utility | Extender P4 runtime for retained concrete interrupt drivers | RETAIN | ACCEPTED | Work 1.a already retained portable ESP-IDF interrupt mechanisms without retaining concrete drivers; this helper is source-compatible unless qualification proves otherwise. |
| SETUP-004.1.c | ESP32 ULP and RTC-domain support used by physical PS/2 input | ESP32-specific input hardware substrate | Onboard VDP remains the physical keyboard and mouse owner for Extender v1 | OMIT | ACCEPTED | ADR-0013 excludes physical PS/2 drivers; porting an incompatible ULP implementation would preserve no selected Extender hardware behavior. |
| SETUP-004.1.c | Portable GPIO configuration and level services | ESP-IDF and Arduino GPIO API | Extender P4 pins selected by retained project hardware profiles | RETAIN | ACCEPTED | Retain normal portable GPIO services for surviving drivers without retaining any stock pin assignment or omitted consumer. |
| SETUP-004.1.c | ESP-IDF SPI bus and device services used by vdp-gl | ESP-IDF SPI platform service | Extender P4 for any retained storage or future project-owned SPI hardware | RETAIN | ACCEPTED | Retain the normal P4 SPI substrate while omitting MCP23S17 and both dormant vdp-gl storage regions. |
| SETUP-004.1.c | FabGL terminal-mode ADC extension services | Omitted terminal peripheral extension | No Extender v1 ADC feature owns this inherited terminal interface | OMIT | ACCEPTED | ADR-0014 omits terminal mode and local operator facilities; retaining deprecated ADC code would preserve no promised behavior. |
| SETUP-004.1.c | vdp-gl task-serialized I2C service | vdp-gl communication driver | No selected Extender v1 I2C device uses this inherited service | OMIT | ACCEPTED | The Author omitted the sole DS3231 consumer; future Extender I2C hardware should use a deliberate project-owned service. |
| SETUP-004.1.c | Direct-register GPIO helper used by the omitted ZDI facility | Omitted maintenance hardware substrate | Onboard VDP retains legacy ZDI maintenance behavior in legacy and applicable cooperative operation | OMIT | ACCEPTED | ADR-0014 excludes ZDI from Extender v1; carrying its direct-register helper adds architecture risk without selected behavior. |
| SETUP-004.1.c | ESP-IDF high-resolution timer and monotonic-clock services | ESP-IDF timing platform service | Extender P4 runtime for whichever consumers survive | RETAIN | ACCEPTED | Preserve the normal P4 monotonic/timer service and qualify behavior per retained consumer rather than replace a standard ESP-IDF facility. |
| SETUP-004.1.c | Stock VDP UART hardware binding and flow-control configuration | Transport hardware | Agon main board and Extender P4 across the adopted parallel-forward and UART1-return harness | REPLACE | ACCEPTED | Prior Work 1.a and harness decisions require Stream-compatible Extender transport adapters while preserving the stock wire contract where strict mode requires it. |
| SETUP-004.1.d | FabGL Canvas and common bitmapped rendering semantics | vdp-gl portable drawing command and state layer | Extender EDP rendering runtime and framebuffer state | RETAIN | ACCEPTED | This is the closest existing semantic seam beneath official VDP commands and preserves mature drawing behavior without rewriting the parser or graphics model. |
| SETUP-004.1.d | Unused FabGL ESP32 composite-video generator | Independently compiled vdp-gl physical video generator | Extender v1 has no selected composite-video output and the onboard VDP provides VGA rather than this facility | OMIT | ACCEPTED | It is neither part of official VDP behavior nor a selected Extender output path. |
| SETUP-004.1.d | Unused FabGL scene compositor helper | Independently compiled vdp-gl software helper | No Extender v1 feature presently selects FabGL Scene | OMIT | ACCEPTED | Carrying and compiling an unused parallel sprite scheduler would confuse it with the retained official VDP sprite path and add unnecessary task/concurrency surface. |
| SETUP-004.1.d | Official VDP screen, mode, palette, and controller integration facade | Header-defined official VDP integration | Extender EDP owns the facade and selected display state in EDP-active modes | RETAIN | ACCEPTED | The accepted VDU inventory requires its complete logical surface, while preserving upstream names and placement minimizes future tagged-release merge work. |
| SETUP-004.1.d | FabGL concrete VGA framebuffer renderers and ESP32 scanout engine | vdp-gl concrete framebuffer and physical output implementation | Extender EDP owns replacement framebuffer production and output sinks; the onboard VDP retains its original VGA hardware in legacy mode | REPLACE | ACCEPTED | Preserve the class-facing and application-visible behavior as closely as practical, reuse proven algorithms where separable, and replace the ESP32 VGA physical engine with an Extender-owned framebuffer/frame-clock backend that can feed network and later local-display sinks. |
| SETUP-004.1.d | Unused FabGL hardware VGA text controller | Independently compiled vdp-gl physical display driver | No Extender v1 behavior selects this independent hardware text controller | OMIT | ACCEPTED | Official VDP text is already rendered through retained Canvas/bitmapped behavior, so porting a second unused physical VGA implementation would add risk without compatibility value. |
| SETUP-004.1.e | FabGL classic-ESP32 DAC, sigma-delta, DMA, timer, and ISR output paths | Fused vdp-gl hardware output backend | Extender P4 owns replacement PCM scheduling and network delivery; no Rev 1 local audio transducer is selected | REPLACE | ACCEPTED | Audio output remains required, but none of the stock DAC/sigma-delta physical implementation or VGA/CVBS selection policy fits the target. |
| SETUP-004.1.e | Official VDP audio protocol, channel, envelope, and sample runtime | Header-defined official VDP audio service | Extender EDP owns audio command state and generated audio in EDP-active modes; the onboard VDP remains independent in legacy mode | RETAIN | ACCEPTED | The accepted VDU inventory keeps the complete audio command surface, status packets, channel semantics, samples, and envelopes; retaining the official implementation minimizes upstream merge divergence while isolating only its concrete output dependency. |
| SETUP-004.1.e | FabGL waveform generation, channel attachment, and PCM mixing core | vdp-gl logical synthesis and mixing service | Extender EDP synthesis runtime produces PCM for whichever Extender output sink is active | RETAIN | ACCEPTED | These mature synthesis semantics directly implement accepted audio commands; a bounded adaptation exposing mixed PCM avoids rewriting waveforms and channel behavior while permitting a project-owned sink. |
| SETUP-004.1.f | Official VDP keyboard/mouse protocol, event, state, and cursor integration | Header-defined official VDP input integration | The onboard VDP owns Rev 1 physical input while Extender owns the EDP-local compatibility state and display effects required in EDP-exclusive operation | REPLACE | ACCEPTED | Preserve the complete code and semantics needed by later compatibility profiles while replacing the inseparable direct PS/2 device bindings with a project-owned injection adapter. |
| SETUP-004.1.f | vdp-gl keyboard device, virtual-key translation, and layout engine | vdp-gl physical keyboard device and scancode translator | The onboard VDP owns PS/2 keyboard reset scan-code decoding layouts typematic LEDs and physical key state for Rev 1 | OMIT | ACCEPTED | No P4 keyboard is selected and processed events arrive from the onboard owner; compile-time retention would duplicate physical translation and tasks. |
| SETUP-004.1.f | vdp-gl mouse device, delta, absolute-position, and acceleration engine | vdp-gl physical mouse device and positioning engine | The onboard VDP owns PS/2 mouse reset packet decoding sampling resolution scaling and acceleration for Rev 1 | OMIT | ACCEPTED | No P4 mouse is selected and direct retention would duplicate physical processing already performed by the onboard owner; required EDP-local position packet and cursor behavior belongs to the replacement compatibility adapter. |
| SETUP-004.1.f | vdp-gl ESP32 ULP-backed physical PS/2 controller | vdp-gl classic-ESP32 physical acquisition backend | The onboard VDP remains the Rev 1 physical PS/2 controller | OMIT | ACCEPTED | Accepted ADR-0013 and Work 1.c architecture excludes FabGL PS/2 and its incompatible ESP32 ULP substrate; no P4 stub or replacement physical controller is selected. |
| SETUP-004.1.g | vdp-gl WiFi-coupled ICMP ping helper | Independently compiled but dormant vdp-gl network utility | none in the official VDP runtime; future Extender network diagnostics would be project-owned | OMIT | ACCEPTED | Source-filter this dormant helper from the P4 build while retaining it in the pinned vendored vdp-gl tree. |
| SETUP-004.1.g | Stock UART Intel HEX and YMODEM transfer services | Header-defined official VDP maintenance and operator facilities | The onboard VDP retains these maintenance facilities in legacy mode and any cooperative operation that leaves their ordinary VDU path available; Extender has no v1 physical or protocol ownership | OMIT | ACCEPTED | ADR-0014 explicitly excludes Intel HEX and YMODEM from Extender v1. |
| SETUP-004.1.h | vdp-gl classic-ESP32 SD/SPIFFS mount, format, and capacity backends | Fused classic-ESP32 physical filesystem backend in fabutils | Extender P4 owns the DevKit microSD card and any selected local flash filesystem; the Agon main board separately owns its MOS-managed SD card | OMIT | ACCEPTED | Omit this classic-ESP32 backend from the P4 build. |
| SETUP-004.1.h | vdp-gl FileBrowser directory and POSIX-style file operations | Dormant utility region inside the otherwise retained fabutils source | This dormant helper owns no active device or compatibility surface; the separate Extender P4 SD-card capability does not require a FileBrowser API | OMIT | ACCEPTED | Extender does not presently require a file browser, and no official VDP behavior or selected vdp-gl consumer requires this class. |

## Coverage

- `SETUP-004.1.a`: 13 accepted; 0 awaiting Author review
- `SETUP-004.1.b`: 4 accepted; 0 awaiting Author review
- `SETUP-004.1.c`: 10 accepted; 0 awaiting Author review
- `SETUP-004.1.d`: 6 accepted; 0 awaiting Author review
- `SETUP-004.1.e`: 3 accepted; 0 awaiting Author review
- `SETUP-004.1.f`: 4 accepted; 0 awaiting Author review
- `SETUP-004.1.g`: 2 accepted; 0 awaiting Author review
- `SETUP-004.1.h`: 2 accepted; 0 awaiting Author review
