bgates747/agon-extender/docs/tasks/QUAL-004/evidence/mode-controls/mode9-run01/COP16_SETUP/mainboard.png

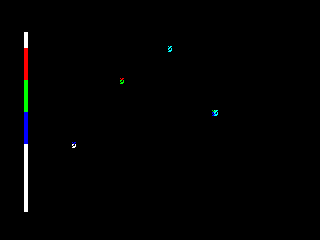
docs/tasks/QUAL-004/evidence/mode-controls/mode9-run01/COP16_SETUP/mainboard.png
