bgates747/agon-extender/hardware/designs/light2-harness-r03/tests/PORT-008-2026-09-10-01-36-43Z/README.md

# ExCom console P4 deployment

The Author returned the bench and SD and authorized proceeding with the paired
installation. The P4's stable USB identity was verified before write and
independent readback verification. The exact candidate starts cleanly and
enumerates the connected PERIBOARD-409. The powered harness remained seated.

This passes P4 deployment/startup only. The SD is prepared with the separately
guarded EMOS v0.1.11 installer and safely unmounted. It preserves the accepted
v0.1.10 image as EMPREV.BIN and archives v0.1.9 as EMV019.BIN, with verified
off-card backups. The agent did not reset or flash Agon. Physical EMOS
installation, ordinary ExCom text/editing and Legacy return remain pending.

Original private device/command logs are retained and hash-bound by the
manifest. The startup excerpt omits machine-specific network/device details.
Follow the adjacent uart-excom-console-r01 procedure after the Author confirms
EMOS installation and the separate non-flashing startup has been restored.
