bgates747/agon-extender/hardware/designs/light2-harness-r03/tests/PORT-015-2026-09-09-21-58-02Z/README.md

The Author reported successful EMOS installation. The consumed SD payload matches
the candidate; rollback is preserved. Matching EMBOOT/check data and the
non-flashing native USB CLI autoexec were staged and the SD safely unmounted.
Physical USB CLI typing remains pending. P4 firmware was not changed in this step.
