bgates747/agon-extender/hardware/designs/light2-harness-r03/tests/PORT-015-2026-09-09-20-50-31Z/README.md

# USB keyboard acquisition observation

Initial acquisition: three lowercase a pairs; Shift+A with Shift released first retains uppercase identity on A release; 1, Enter and Backspace pairs; held a produces one DOWN/UP; unplug while holding Shift+A synthesizes both UP events. Operator clarified no reconnection occurred in this run.

The operator reports corrected data wiring to EXT2.19/20. The unchanged candidate received the keyboard. Removal logs `USB HOST: EP command error: ESP_ERR_INVALID_STATE`; retain this informative diagnostic and investigate before claiming the no-fault gate. Opening serial observed application startup; its cause is unresolved. No restart was observed after host readiness within this recording. Full raw serial and private metadata are retained locally; the published excerpt includes all USB lines and error-level lines. This is acquisition evidence, not EMOS keyboard integration.

## Wiring-state correction — 2026-09-09T20:58:50+00:00

The Author clarified that Agon was powered during these USB captures, but the Agon harness was not connected to the P4 right-side header (the same side as the USB connections). This supersedes the earlier assumption of a fully seated Agon/P4 harness for these runs. Native USB observations remain valid for this reported wiring state; simultaneous operation with the full Agon harness attached was not tested. The relation, if any, to the unplug diagnostic remains unestablished. No reconnection or hardware operation is implied by this correction.

Review 2026-09-09T21:06:51+00:00: the [pinned-source trace](../usb-keyboard-unplug-review.md) explains the removal diagnostic; it no longer blocks the bounded acquisition result. Earlier observations and partial outcome remain intact.
