bgates747/agon-extender/hardware/designs/light2-harness-r03/tests/PORT-014-2026-09-08-19-52-44Z/README.md

# Repeatable receiver: first captured exchange

P4 stages pass and the Author reports the browser banner. Independent offline
review confirms the exact 35-byte request and 8001A6 response, framing and flow
control. The original capture hash and serial verdict verify.

Acquisition stopped at 119128764 of 240000000 samples: 4.9636985 seconds at
24MHz. Final waveform quiet tail is 4.391214 seconds; both acquisition and the
five-second tail checks remain failed. Serial monitoring was clean for 7.004348
seconds after PASS. No exception acceptance or repeated-reset result is claimed.

The Author requested richer output next: clear screen, the EMOS-to-EDP banner,
and decimal 1 through 10 on separate lines, generated from numeric values.
