bgates747/agon-extender/hardware/designs/light2-harness-r03/tests/PORT-014-2026-09-08-19-28-52Z/README.md

# EMOS v0.7.0 installation media prepared

The clean candidate passes configured/linked/runtime checks and same-build
ordinary, bad-SD and no-peer emulator checks. The Author accepted the draft's
graphical review and authorized this SD preparation.

The verified guarded installer is on the safely unmounted card. Working v0.6.0
is EMPREV.BIN; older v0.5.0/v0.4.0/v0.3.0/v0.2.0 images remain archived on
card. All affected old files were backed up and verified off-card.

Insert into the powered Agon and press/release reset once. Expect flash CRC
verification and Done. The next boot's missing EMNEW.BIN rename is the reflash
guard. Return the SD after successful installation for separate same-build
smoke/VDPTEXT media. Keep both boards powered and ribbons seated.

The P4 candidate is built but has not been deployed. Physical installation and
the paired UART/browser test remain pending.
