bgates747/agon-extender/hardware/designs/light2-harness-r03/tests/PORT-014-2026-09-08-19-32-11Z/README.md

# EMOS v0.7.0 installed; test media prepared

The Author reported a successful flash. The consumed SD payload matches the
clean v0.7.0 candidate exactly; EMNEW.BIN is absent and verified working v0.6.0
and v0.2.0 rollbacks remain intact. The installer is replaced by the same-build
SD/CLOCK smoke and EMOS VDPTEXT startup; no flash command remains.

The card is safely unmounted. The P4 visible-text candidate still requires
separate deployment before the paired UART/browser test. The Author should
insert the card without resetting Agon until the paired capture is ready.
