bgates747/agon-extender/hardware/designs/light2-harness-r03/tests/PORT-013-2026-09-08-17-55-37Z/README.md

# EMOS v0.6.0 installation media prepared

The clean candidate passes the full configured/linked/runtime gate, 71 host
tests, stock/EMOS ordinary and bad-SD smoke, and bounded no-peer General Poll
return. The Author accepted the preceding draft's graphical behavior and
approved source freeze/preparation. The manifest identifies the candidate.

The guarded installer and firmware are verified on SD, which is safely
unmounted. Working v0.5.0 remains as EMPREV.BIN; v0.4.0 is preserved as
EMV040.BIN, v0.3.0 as EMV030.BIN and v0.2.0 as EMBACK.BIN. All are backed
up off-card.

Insert the card into the powered Agon and press/release reset once. Expect
flash CRC verification and Done. The following boot stops at the missing
EMNEW.BIN rename; that is the reflash guard. After successful installation,
return the SD for the separate same-build smoke/VDPPOLL autoexec.

The matching P4 candidate is built, staged and hash-verified, but has not been
flashed. No General Poll capture has run. Physical installation remains pending;
keep both boards powered and ribbons seated.
