bgates747/agon-extender/hardware/designs/light2-harness-r03/tests/PORT-012-2026-09-08-17-16-35Z/README.md

# Target-baud P4 candidate deployed

The Author authorized flashing. The candidate factory image was written and
independently verified on the expected P4 v1.3. Startup confirms the exact
candidate identity, RX22/TX12/CTS23/RTS11, 1,152,000 baud and empty WAIT with
CTS HIGH. This passes installation/readiness only; the paired UARTFLOW run
and waveform qualification remain pending. Private device/command logs remain
in ignored bench records. The harness stayed seated; no Agon reset occurred.
