bgates747/agon-extender/docs/tasks/REMOTE-005/A08-RESULTS.md

# R05-A08 — local WebDAV adapter results

The HTTP adapter, real wire client and staged file orchestration now pass local
checks against the actual EMOSlet engine. No bench access, flashing, emulator
changes or production selection changes occurred. **A08 remains open:** runtime
admission, media ownership and a dedicated listener/worker must still be wired;
this is not an enabled or native-client-qualified WebDAV endpoint.
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
