bgates747/agon-extender/docs/tasks/NET-001/results/frame.png

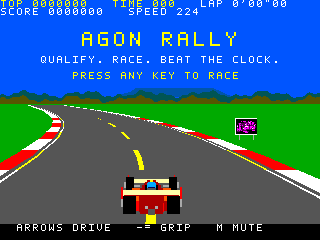
docs/tasks/NET-001/results/frame.png
