bgates747/agon-extender/docs/tasks/PORT-004/audio-framing/results/rally-unmuted.png

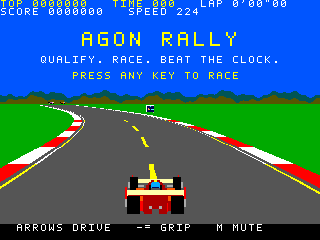
docs/tasks/PORT-004/audio-framing/results/rally-unmuted.png
