bgates747/agon-extender/docs/tasks/QUAL-003/nurples-parity/results/r38-free.png

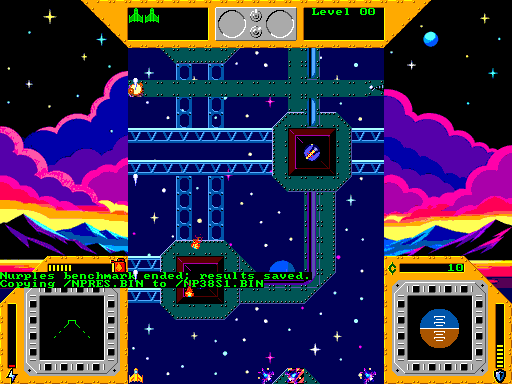
docs/tasks/QUAL-003/nurples-parity/results/r38-free.png
