bgates747/agon-extender/docs/tasks/QUAL-003/nurples-parity/results/row-r30-game.png

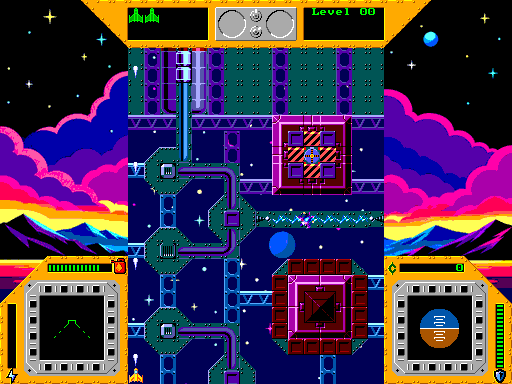
docs/tasks/QUAL-003/nurples-parity/results/row-r30-game.png
