bgates747/agon-extender/docs/tasks/QUAL-003/rally-excom/rx09/results/rally-smoke.png

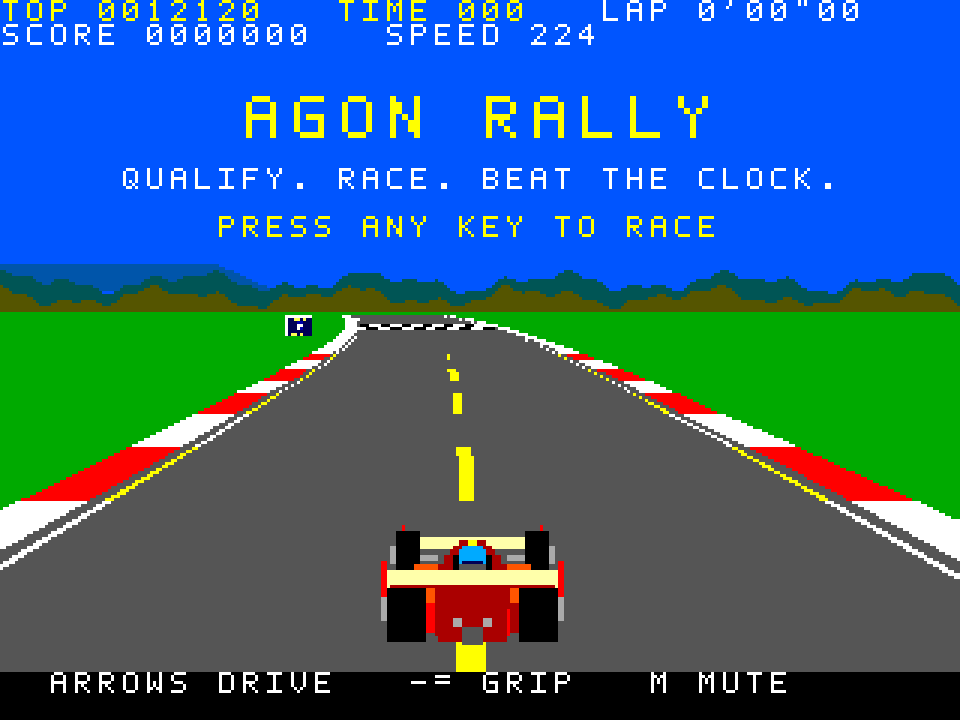
docs/tasks/QUAL-003/rally-excom/rx09/results/rally-smoke.png
