bgates747/agon-extender/docs/tasks/QUAL-003/suite/UPSTREAM-TODO.md

> Upstream snapshot; historical reference only. QUAL-003 owns this adaptation.

# Extender demos TODO

This is the only unfinished-work list for these demos. Completed work and
validation evidence belong in `docs/development/`.

1. [ ] EXT-003 — Obtain Author visual review of the complete, deployed
   [Shapes tour](docs/tasks/EXT-003.md). All 24 pages are implemented and
   exercised in the reference emulator; SHP-11/12/23 retain the documented
   [reference discrepancies](docs/reference-observations.md). SHP-01/02 and
   keypress/Escape controls are already visually accepted.
