bgates747/agon-extender/hardware/designs/light2-harness-r03/schematic.kicad_sch

## KiCad design hardware/designs/light2-harness-r03/schematic.kicad_sch (2026-09-07)

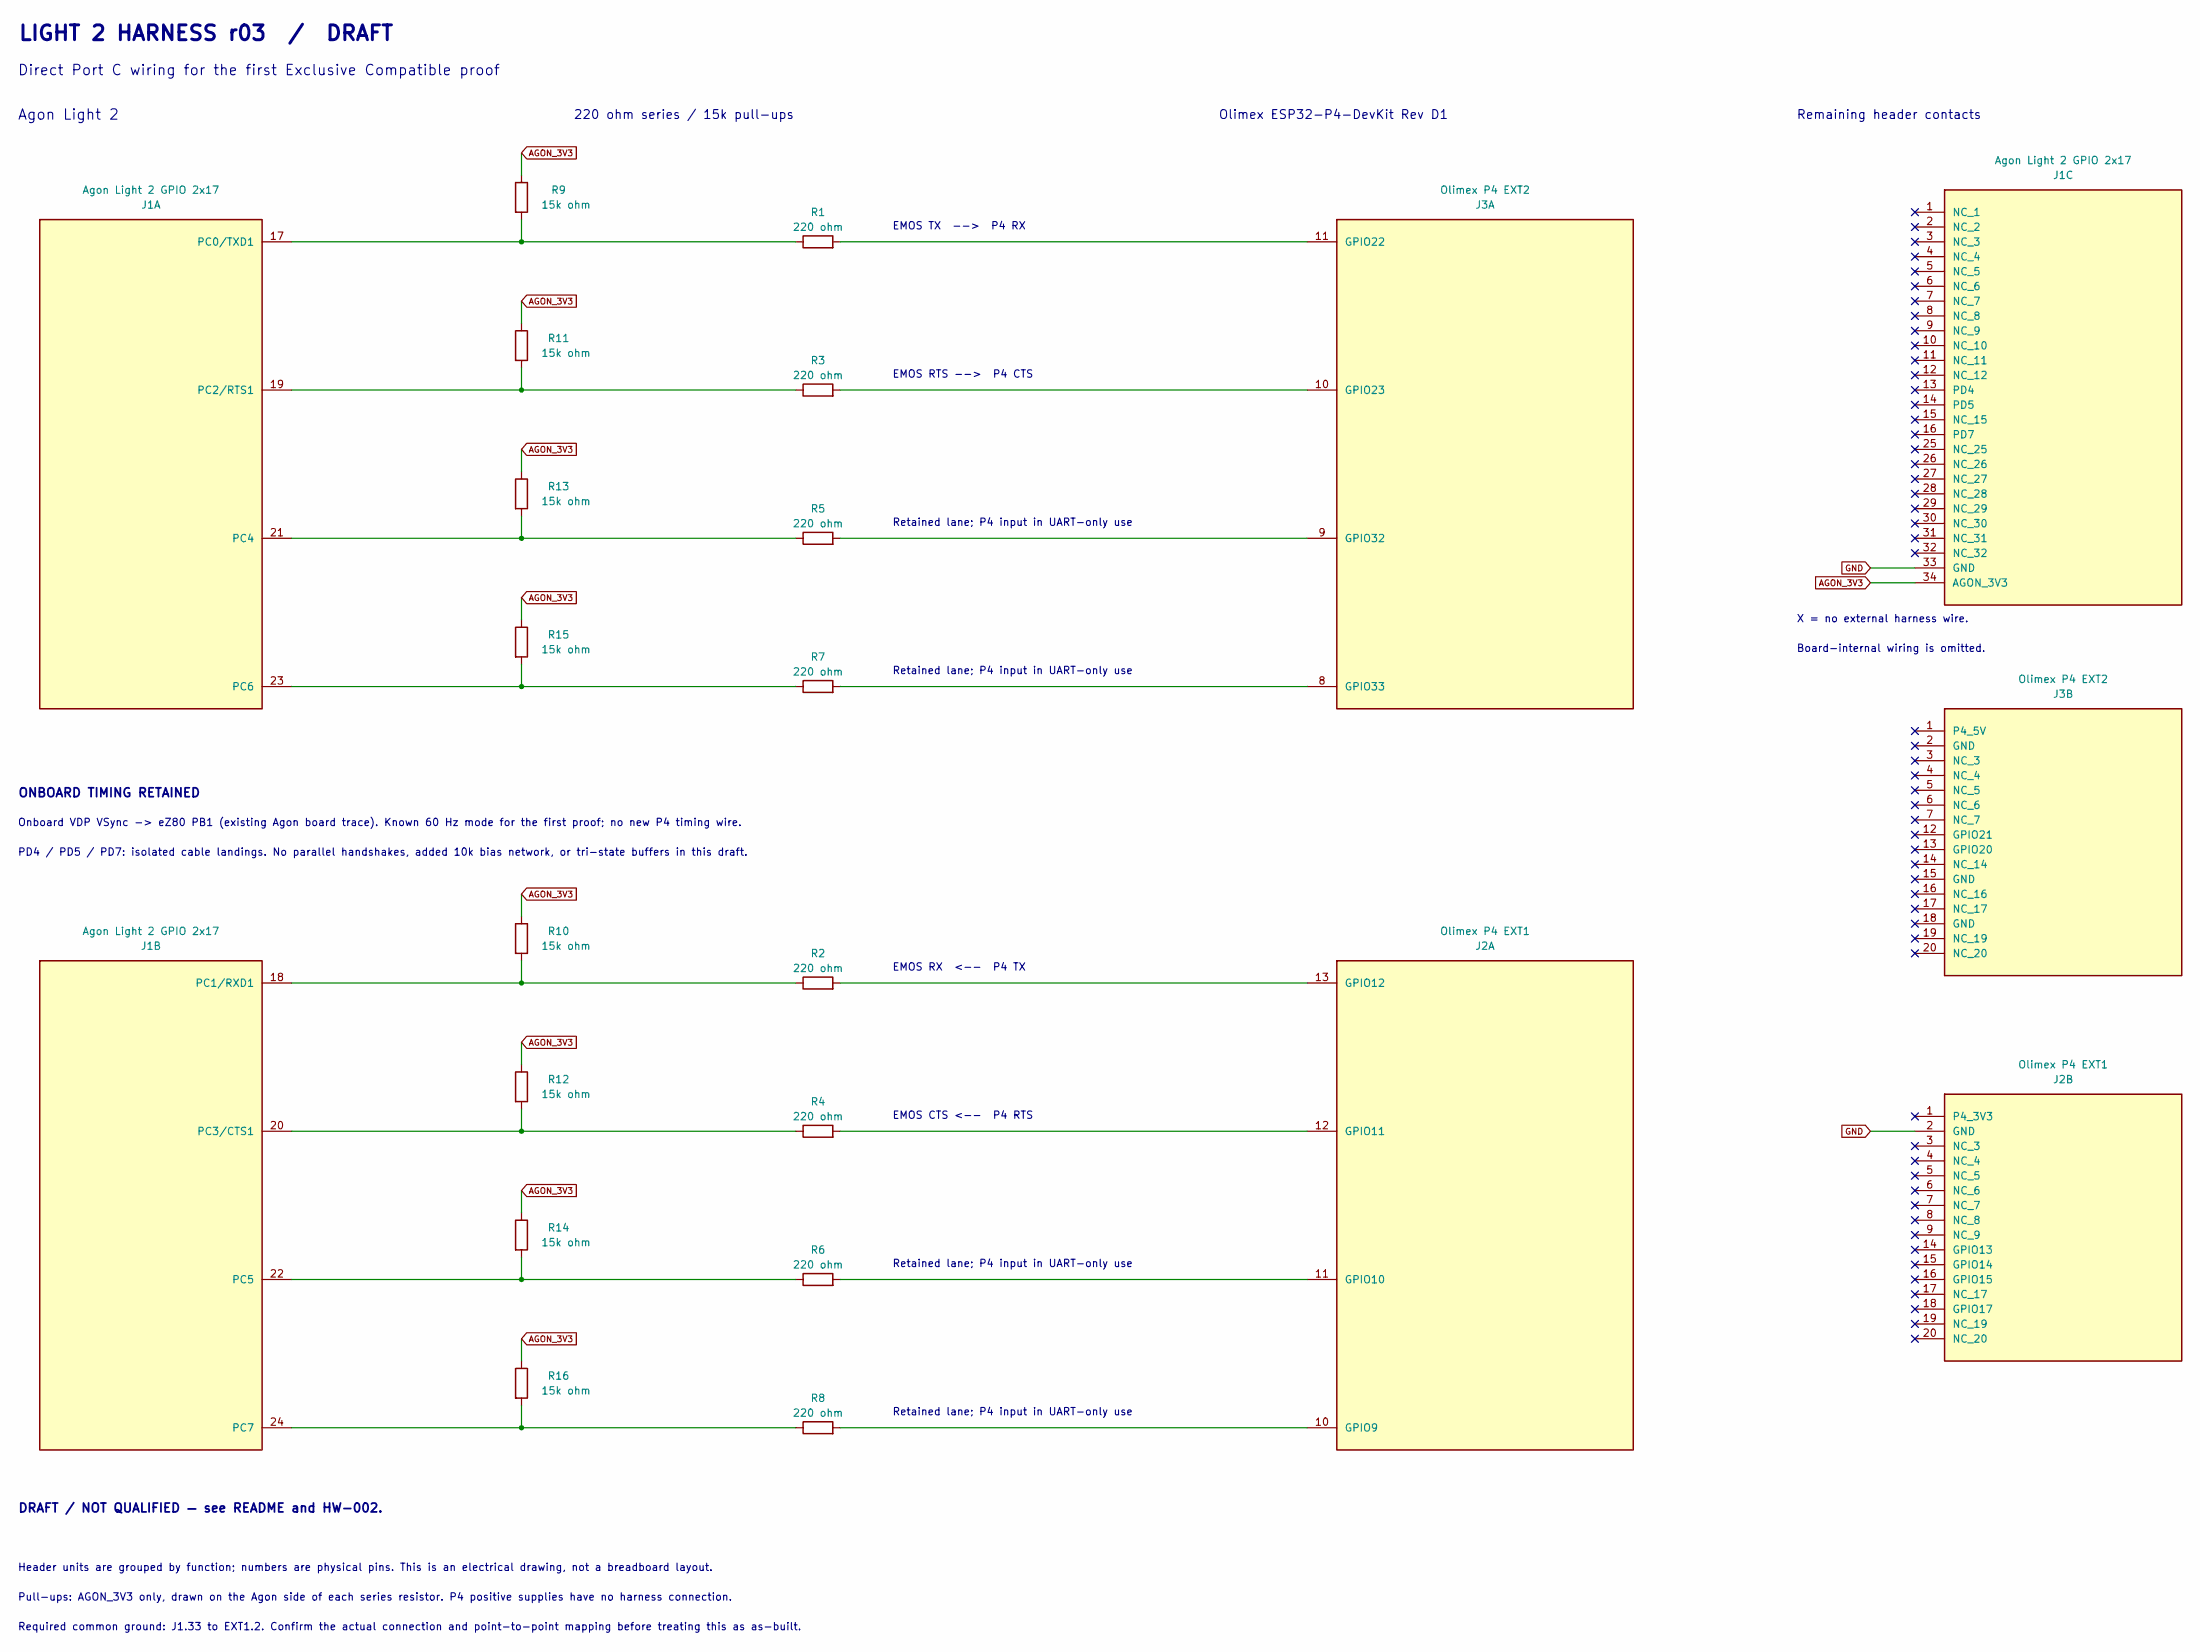
[picture p71: schematic schematic.kicad_sch]

Parts:
J1: Agon Light 2 GPIO 2x17
J2: Olimex P4 EXT1
J3: Olimex P4 EXT2
R1, R2, R3, R4, R5, R6, R7, R8: 220 ohm
R9, R10, R11, R12, R13, R14, R15, R16: 15k ohm

Connections:
AGON_3V3: J1.34 (AGON_3V3), R9.1, R10.1, R11.1, R12.1, R13.1, R14.1, R15.1, R16.1
GND: J1.33 (GND), J2.2 (GND)
unnamed: J1.17 (PC0/TXD1), R1.1, R9.2
unnamed: J1.18 (PC1/RXD1), R2.1, R10.2
unnamed: J1.19 (PC2/RTS1), R3.1, R11.2
unnamed: J1.20 (PC3/CTS1), R4.1, R12.2
unnamed: J1.21 (PC4), R5.1, R13.2
unnamed: J1.22 (PC5), R6.1, R14.2
unnamed: J1.23 (PC6), R7.1, R15.2
unnamed: J1.24 (PC7), R8.1, R16.2
unnamed: J2.10 (GPIO9), R8.2
unnamed: J2.11 (GPIO10), R6.2
unnamed: J2.12 (GPIO11), R4.2
unnamed: J2.13 (GPIO12), R2.2
unnamed: J3.8 (GPIO33), R7.2
unnamed: J3.9 (GPIO32), R5.2
unnamed: J3.10 (GPIO23), R3.2
unnamed: J3.11 (GPIO22), R1.2

Notes on the sheet:
EMOS TX --> P4 RX
EMOS RTS --> P4 CTS
Retained lane; P4 input in UART-only use
EMOS RX <-- P4 TX
EMOS CTS <-- P4 RTS
LIGHT 2 HARNESS r03 / DRAFT
Direct Port C wiring for the first Exclusive Compatible proof
Agon Light 2
220 ohm series / 15k pull-ups
Olimex ESP32-P4-DevKit Rev D1
Remaining header contacts
Header units are grouped by function; numbers are physical pins. This is an electrical drawing, not a breadboard layout.
Pull-ups: AGON_3V3 only, drawn on the Agon side of each series resistor. P4 positive supplies have no harness connection.
Required common ground: J1.33 to EXT1.2. Confirm the actual connection and point-to-point mapping before treating this as as-built.
ONBOARD TIMING RETAINED
Onboard VDP VSync -> eZ80 PB1 (existing Agon board trace). Known 60 Hz mode for the first proof; no new P4 timing wire.
PD4 / PD5 / PD7: isolated cable landings. No parallel handshakes, added 10k bias network, or tri-state buffers in this draft.
X = no external harness wire.
Board-internal wiring is omitted.
DRAFT / NOT QUALIFIED — see README and HW-002.
