bgates747/agon-extender/docs/tasks/HW-001/electrical-model/generated/topology-example.kicad_sch

## KiCad design docs/tasks/HW-001/electrical-model/generated/topology-example.kicad_sch (2026-08-29)

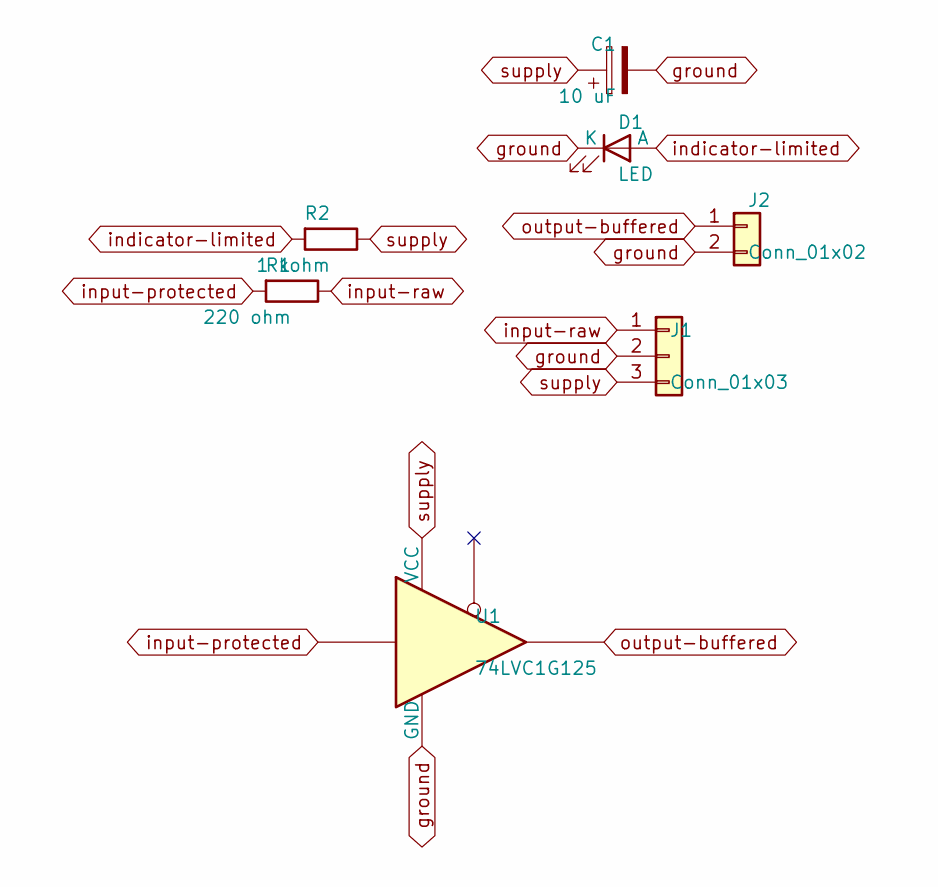
[picture p72: schematic topology-example.kicad_sch]

Parts:
C1: 10 uF
D1: LED
J1: Conn_01x03
J2: Conn_01x02
R1: 220 ohm
R2: 1 kohm
U1: 74LVC1G125

Connections:
ground: C1.2, D1.1 (K), J1.2, J2.2, U1.3 (GND)
indicator-limited: D1.2 (A), R2.2
input-protected: R1.2, U1.2
input-raw: J1.1, R1.1
output-buffered: J2.1, U1.4
supply: C1.1, J1.3, R2.1, U1.5 (VCC)
