bgates747/agon-extender/hardware/designs/light2-harness-r02/signal-views/generated/01_schematic_power-domains.kicad_sch

## KiCad design hardware/designs/light2-harness-r02/signal-views/generated/01_schematic_power-domains.kicad_sch (2026-09-04)

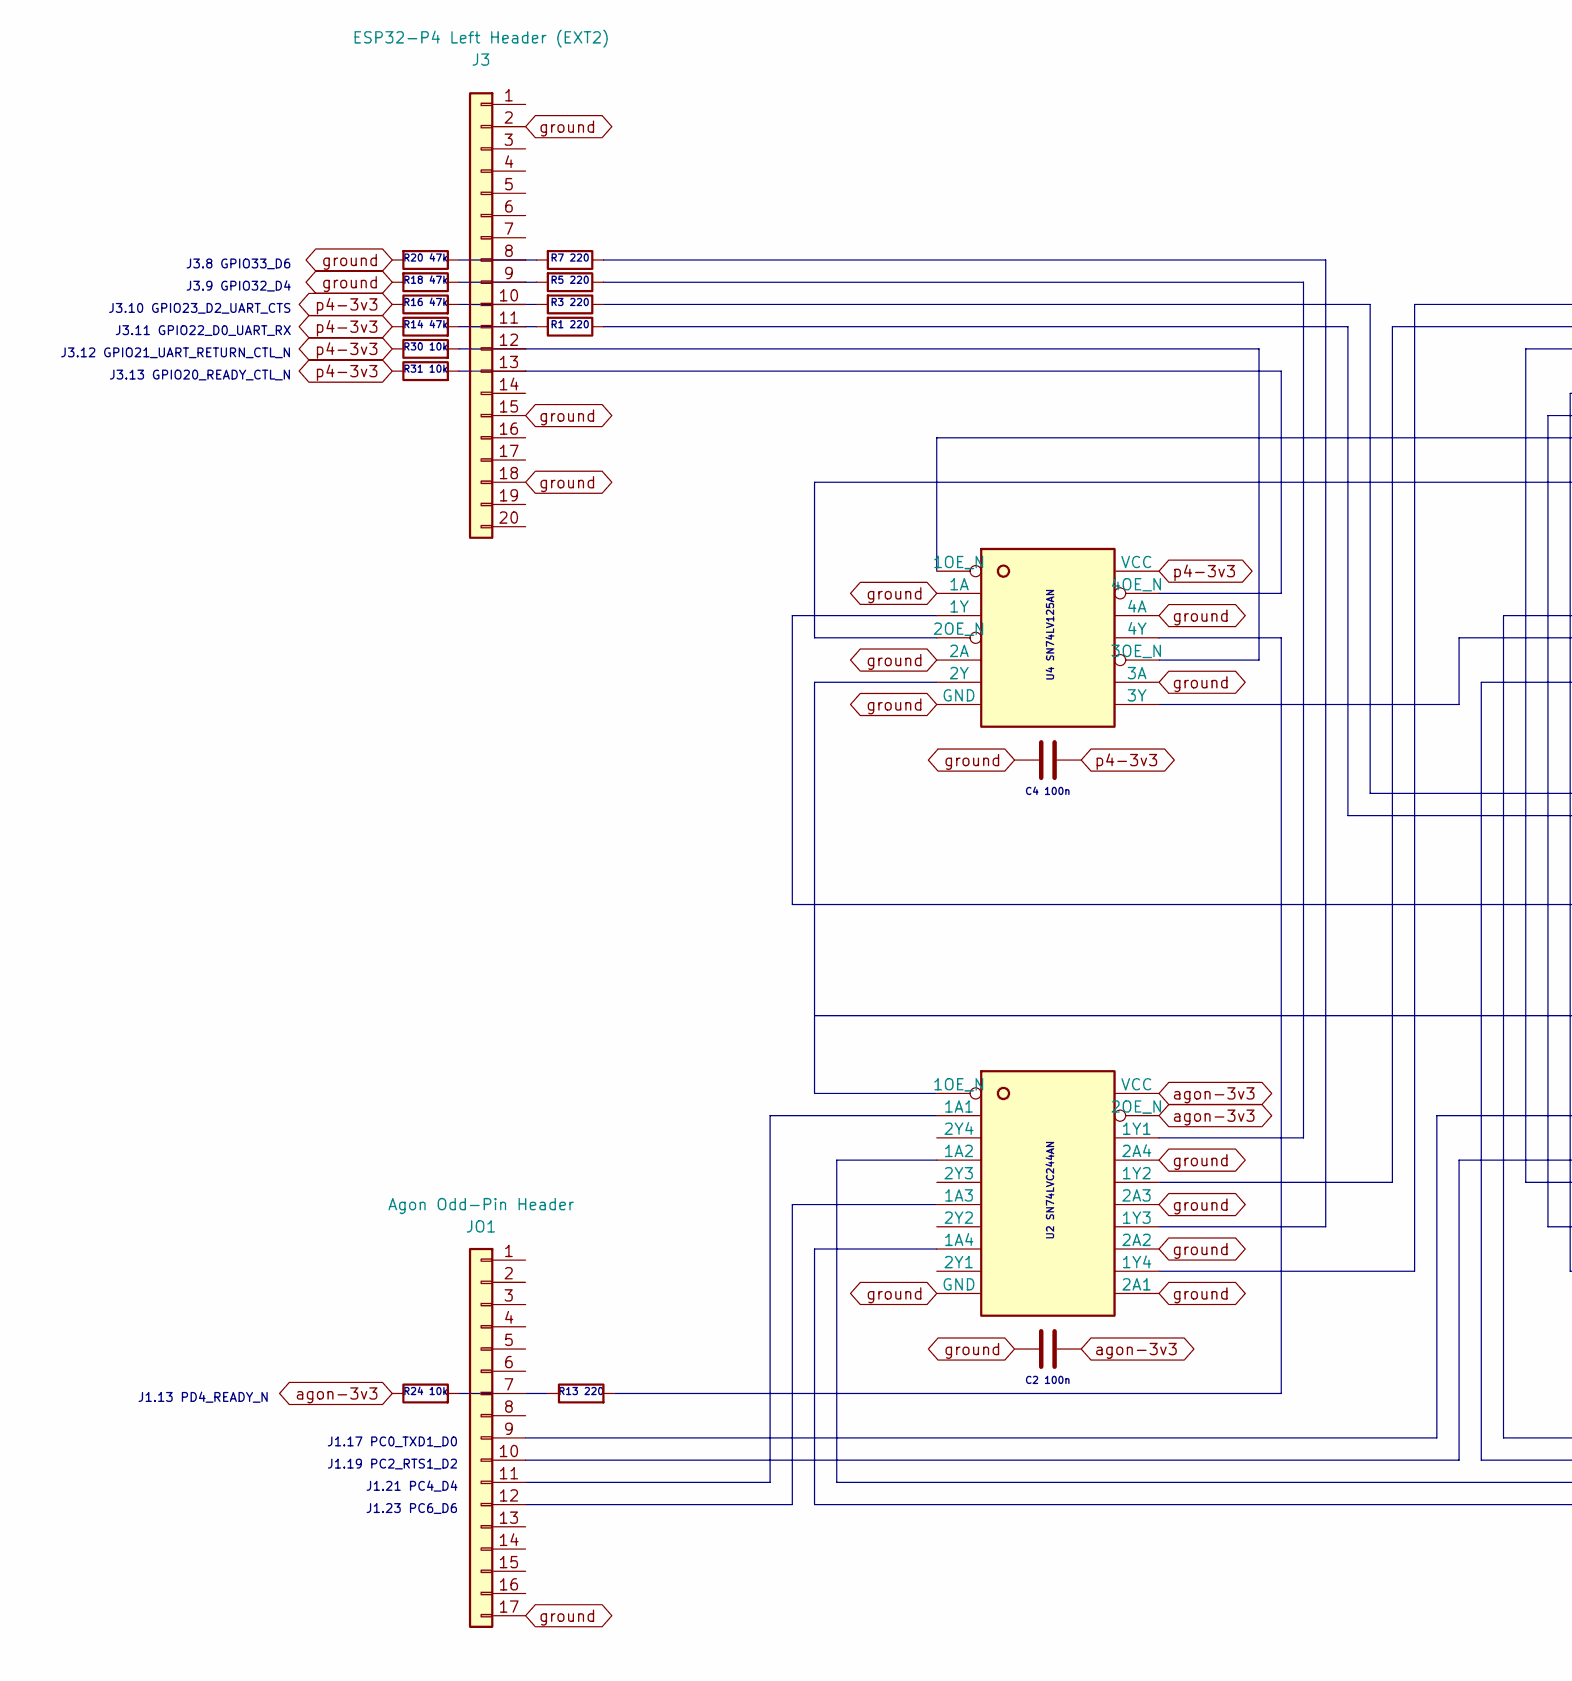
[picture p73: schematic 01_schematic_power-domains.kicad_sch, part in row 1, column 1]

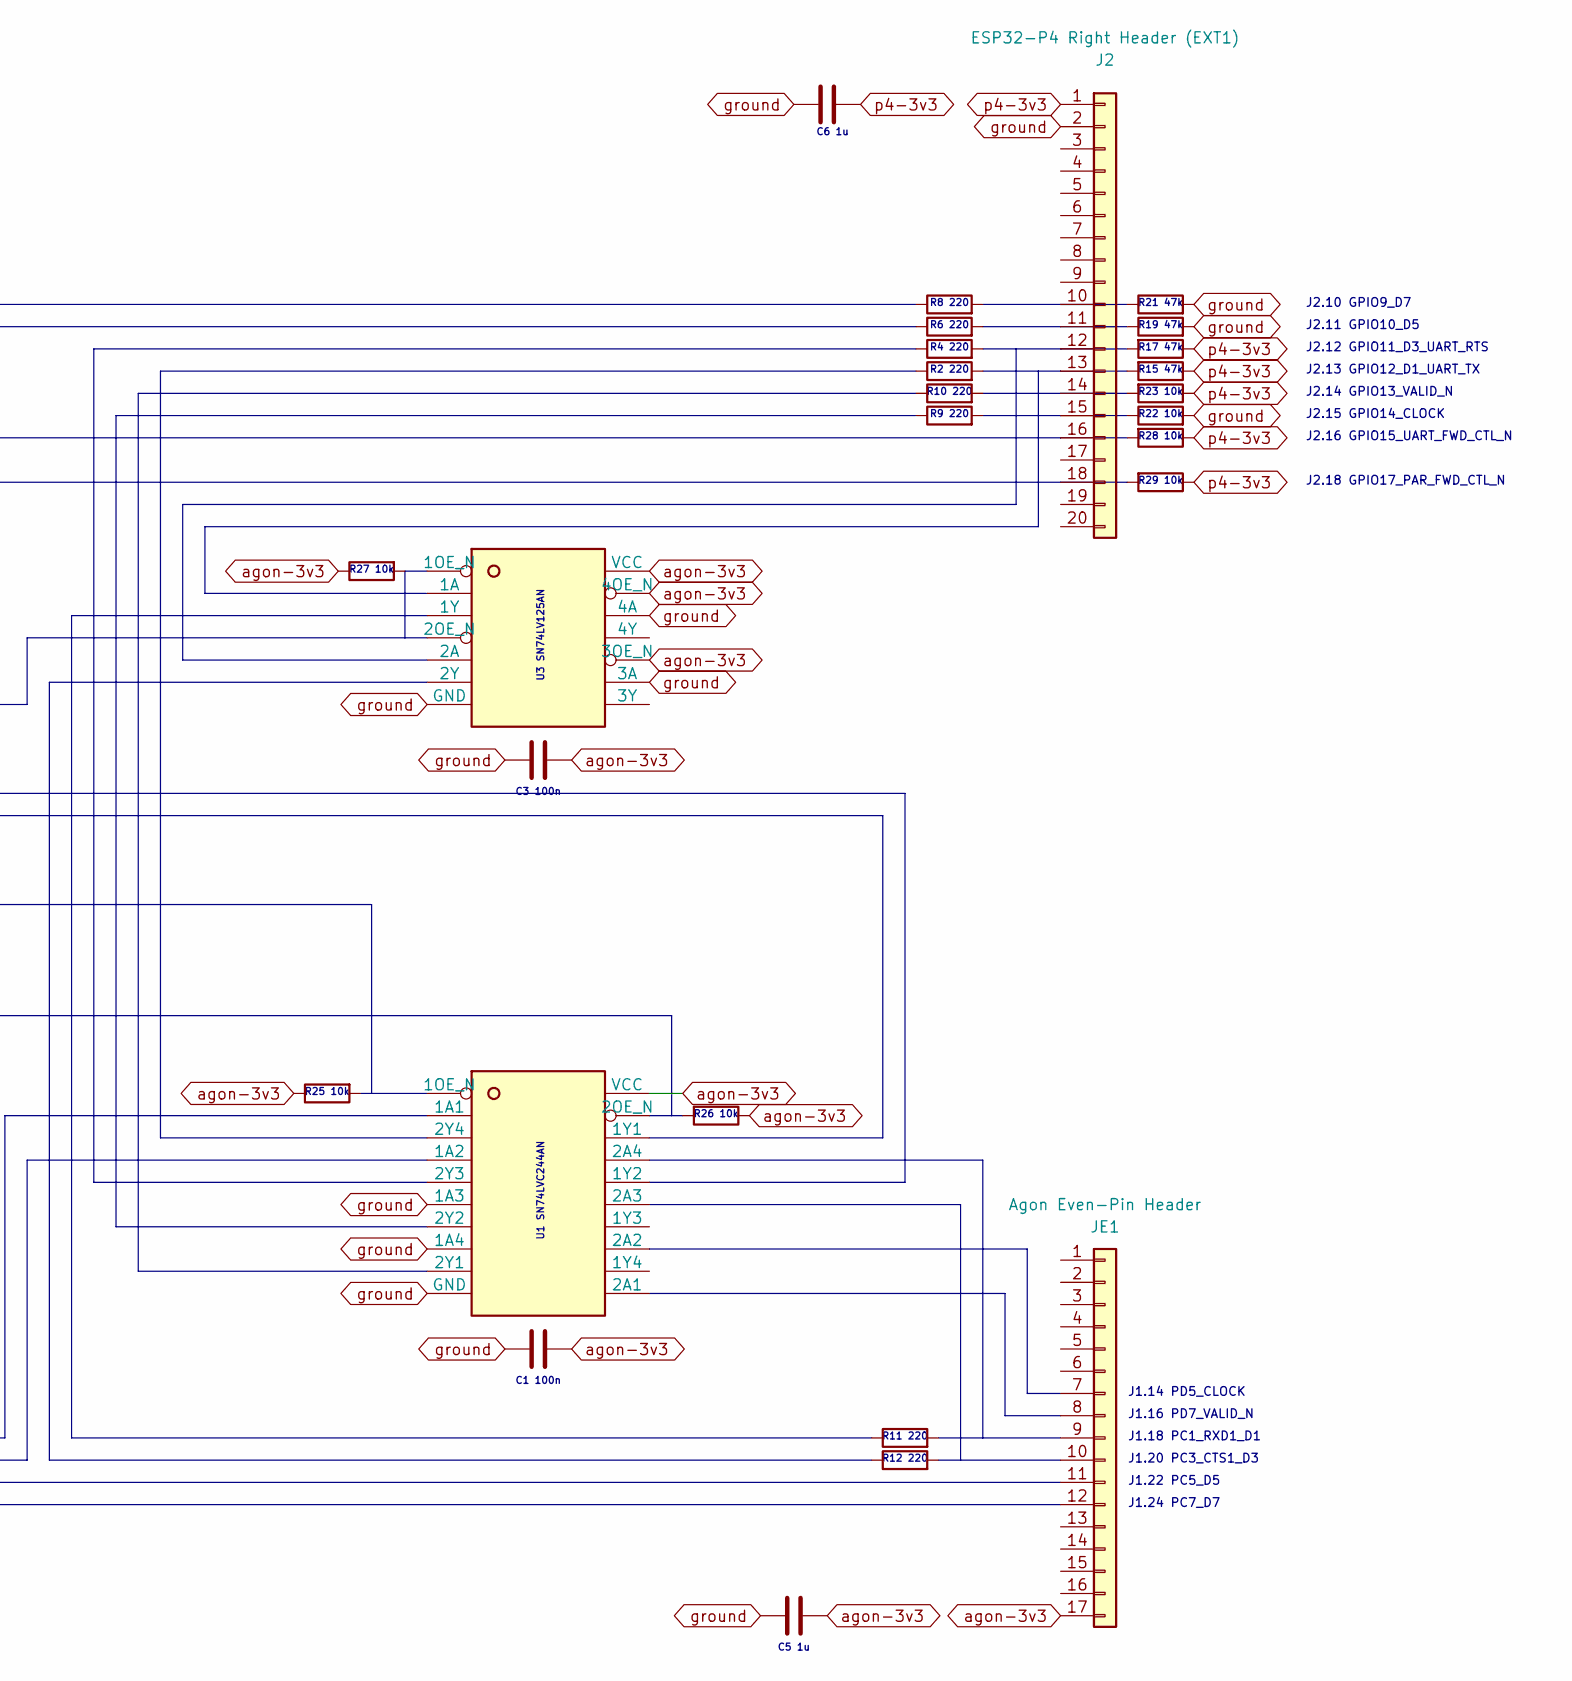
[picture p74: schematic 01_schematic_power-domains.kicad_sch, part in row 1, column 2]

Parts:
C1, C2, C3, C4: 100 nF
C5, C6: 1 uF
J2: ESP32-P4 Right Header (EXT1)
J3: ESP32-P4 Left Header (EXT2)
JE1: Agon Even-Pin Header
JO1: Agon Odd-Pin Header
R1, R2, R3, R4, R5, R6, R7, R8, R9, R10, R11, R12, R13: 220 ohm
R14, R15, R16, R17, R18, R19, R20, R21: 47 kohm
R22, R23, R24, R25, R26, R27, R28, R29, R30, R31: 10 kohm
U1, U2: SN74LVC244AN; DIP-20_W7.62mm
U3, U4: SN74LV125AN; DIP-14_W7.62mm

Connections:
agon-3v3: C1.2, C2.2, C3.2, C5.2, JE1.17, R24.1, R25.1, R26.1, R27.1, U1.20 (VCC), U2.19 (2OE_N), U2.20 (VCC), U3.10 (3OE_N), U3.13 (4OE_N), U3.14 (VCC)
ground: C1.1, C2.1, C3.1, C4.1, C5.1, C6.2, J2.2, J3.2, J3.15, J3.18, JO1.17, R18.2, R19.2, R20.2, R21.2, R22.2, U1.6 (1A3), U1.8 (1A4), U1.10 (GND), U2.10 (GND), U2.11 (2A1), U2.13 (2A2), U2.15 (2A3), U2.17 (2A4), U3.7 (GND), U3.9 (3A), U3.12 (4A), U4.2 (1A), U4.5 (2A), U4.7 (GND), U4.9 (3A), U4.12 (4A)
p4-3v3: C4.2, C6.1, J2.1, R14.1, R15.1, R16.1, R17.1, R23.1, R28.1, R29.1, R30.1, R31.1, U4.14 (VCC)

Notes on the sheet:
U1 SN74LVC244AN
J1.13 PD4_READY_N
J1.24 PC7_D7
R18 47k
J2.14 GPIO13_VALID_N
J3.13 GPIO20_READY_CTL_N
R22 10k
J2.18 GPIO17_PAR_FWD_CTL_N
R31 10k
U3 SN74LV125AN
R30 10k
R13 220
C1 100n
J3.8 GPIO33_D6
J2.16 GPIO15_UART_FWD_CTL_N
R9 220
R21 47k
R15 47k
C3 100n
J1.19 PC2_RTS1_D2
J3.12 GPIO21_UART_RETURN_CTL_N
J2.11 GPIO10_D5
R24 10k
J2.12 GPIO11_D3_UART_RTS
R17 47k
J2.10 GPIO9_D7
J1.22 PC5_D5
R20 47k
J3.9 GPIO32_D4
C6 1u
R4 220
R10 220
R1 220
R11 220
R19 47k
J1.18 PC1_RXD1_D1
R29 10k
R28 10k
U4 SN74LV125AN
J3.11 GPIO22_D0_UART_RX
R27 10k
U2 SN74LVC244AN
R26 10k
R16 47k
J1.23 PC6_D6
R8 220
R12 220
J2.15 GPIO14_CLOCK
C4 100n
R6 220
R14 47k
R3 220
J1.20 PC3_CTS1_D3
R23 10k
R7 220
J1.16 PD7_VALID_N
C5 1u
R2 220
R25 10k
J1.14 PD5_CLOCK
J2.13 GPIO12_D1_UART_TX
J3.10 GPIO23_D2_UART_CTS
R5 220
J1.17 PC0_TXD1_D0
J1.21 PC4_D4
C2 100n
