bgates747/agon-extender/qualification/render_load_controls.py

#!/usr/bin/env python3
"""Run supplemental presentation controls with benchmark-specific P4 hooks absent.

The caller installs/verifies the preserved ordinary image and proves CLI first.
This runner never selects or flashes firmware. Selection files retain affected
runs/cases and their setup prefixes. Ordinary serial logging can suppress a
zero-update window; silence is therefore inconclusive output evidence.
"""
import argparse,datetime,hashlib,json,os,select,sys,termios,threading,time,tty,urllib.request
from pathlib import Path
from render_load import Bench,utc,digest
HOST_SOURCE_SHA256=digest(Path(__file__).read_bytes())

def write(path,value):path.write_text(json.dumps(value,indent=2)+'\n')
def status(b,path):
 with urllib.request.urlopen(b.config['p4']+path,timeout=5) as r:return json.load(r)

def verify_image(config,image):
 manifest=json.loads((image/'manifest.json').read_text())
 current=json.loads(Path(config['installation_record']).read_text())
 receipt=json.loads(Path(current['receipt']).read_text())
 assert current['variant']=='ordinary-hdmi' and current['build_id']==manifest['build_id']==receipt['build_id'] and receipt['outcome']=='pass'
 assert manifest['idf_commit']=='b774170ff46c393eeb5e495ea37936038d3f4f4f' and manifest['display_output']=='hdmi'
 compile_path=image/'build/compile_commands.json'
 expected=next(a['sha256'] for a in manifest['artifacts'] if a['path'].endswith('/compile_commands.json'))
 assert digest(compile_path.read_bytes())==expected
 commands=json.loads(compile_path.read_text())
 relevant=[c for c in commands if any(c['file'].endswith(n) for n in ('hdmi_output.cpp','stock_p4_service.cpp','stock_native_access.cpp','video.ino.cpp'))]
 assert len(relevant)>=3
 for command in relevant:
  text=command.get('command',' '.join(command.get('arguments',[])))
  assert 'AGON_EXTENDER_RENDER_BENCHMARK' not in text and 'AGON_EXTENDER_BENCH_HOLD' not in text and 'AGON_EXTENDER_BENCH_OFF' not in text
 assert all('AGON_EXTENDER_RENDER_BENCHMARK' not in c.get('command',' '.join(c.get('arguments',[]))) for c in commands)
 return dict(build_id=manifest['build_id'],installation_receipt=current['receipt'],manifest_sha256=digest((image/'manifest.json').read_bytes()),compile_commands_sha256=expected,checked_translation_units=[Path(c['file']).name for c in relevant],scope='Benchmark-specific window/phase/marker hooks absent; ordinary image logging retained')

class PassiveSerial:
 def __init__(self,config,out):
  self.out=out;self.stop=threading.Event();self.errors=[];self.count=0
  port=Path(config['serial_port']);node=port.resolve(strict=True)
  device=(Path('/sys/class/tty')/node.name/'device').resolve()
  serials=[(p/'serial').read_text().strip() for p in device.parents if (p/'serial').is_file()]
  assert config['usb_serial'] in serials
  self.fd=os.open(str(port),os.O_RDWR|os.O_NOCTTY|os.O_NONBLOCK)
  tty.setraw(self.fd,termios.TCSANOW);cfg=termios.tcgetattr(self.fd)
  cfg[2]=(cfg[2]|termios.CLOCAL|termios.CREAD)&~termios.HUPCL;cfg[4]=cfg[5]=termios.B115200
  termios.tcsetattr(self.fd,termios.TCSANOW,cfg)
  self.started=time.monotonic();self.utc=datetime.datetime.now(datetime.timezone.utc).isoformat()
  self.thread=threading.Thread(target=self.read,daemon=True);self.thread.start()
 def read(self):
  try:
   with (self.out/'passive-serial.log').open('wb',buffering=0) as log,(self.out/'serial-chunks.jsonl').open('w') as chunks:
    while not self.stop.is_set() and time.monotonic()-self.started<7200:
     if select.select([self.fd],[],[],.25)[0]:
      data=os.read(self.fd,8192)
      if not data:raise RuntimeError('Serial endpoint closed during control')
      chunks.write(json.dumps(dict(utc=datetime.datetime.now(datetime.timezone.utc).isoformat(),elapsed_seconds=time.monotonic()-self.started,offset=self.count,bytes=len(data)))+'\n');chunks.flush()
      log.write(data);self.count+=len(data)
  except Exception as error:self.errors.append(repr(error))
 def close(self):
  self.stop.set();self.thread.join(3);os.close(self.fd)
  path=self.out/'passive-serial.log'
  return dict(started_utc=self.utc,elapsed_seconds=time.monotonic()-self.started,bytes=self.count,sha256=digest(path.read_bytes()) if path.exists() else None,errors=self.errors,serial_commands_sent=False,modem_lines_toggled=False,clock_scope='Host arrival timestamps; serial backlog and ordinary report windows prevent exact per-case output attribution')
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
