bgates747/agon-extender/qualification/render_load_plots.py

#!/usr/bin/env python3
"""Build an offline interactive review of already analysed rendering measurements.

This tool reads local analysis only. It cannot invoke fixtures or contact a bench.
Paired passes stay paired; absent/failing measurements are never replaced by zero.
"""
import argparse
import datetime
import hashlib
import json
import math
from pathlib import Path

ROOT = Path(__file__).resolve().parents[1]
ASSETS = Path(__file__).with_name('render_load_web')
MODES = {20: (512, 384, 64, False), 8: (320, 240, 64, False),
         136: (320, 240, 64, True), 21: (512, 384, 16, False),
         149: (512, 384, 16, True)}
INPUTS = ('comparison.json', 'cases.json', 'coverage.json', 'execution-audit.json',
          'zero-submissions.json', 'excluded.json')


def digest(data):
    return hashlib.sha256(data).hexdigest()


def load_payload(analysis):
    """Keep matched comparisons and matching raw-derived run references together."""
    objects, hashes = {}, {}
    snapshot = analysis / 'pause-manifest.json'
    expected = json.loads(snapshot.read_text())['analysis_files_sha256'] if snapshot.exists() else {}
    for name in INPUTS:
        data = (analysis / name).read_bytes()
        hashes[name] = digest(data)
        if expected and hashes[name] != expected.get(name):
            raise ValueError(f'Snapshot hash mismatch: {name}')
        objects[name] = json.loads(data)
    audit = objects['execution-audit.json']
    if not audit['raw_provenance_complete']:
        raise ValueError('Raw provenance audit has unresolved issues')
    contract = json.loads((ROOT / 'tests/performance/render_load/contract-r04.json').read_text())
    if objects['coverage.json']['suite'] != contract['identity'] or audit['suite'] != contract['identity']:
        raise ValueError('Analysis does not describe the frozen r04 suite')
    allowed = {w['family']: w['variants'] for w in contract['workloads']}
    rows, seen = [], set()
    for original in objects['comparison.json']:
        row = dict(original)
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
